Board-Folk/TRS80IUS/v1.1/Kicad/TR80IUS_VRAM.kicad_sch

## KiCad design v1.1/Kicad/TR80IUS_VRAM.kicad_sch (2023-12-29)

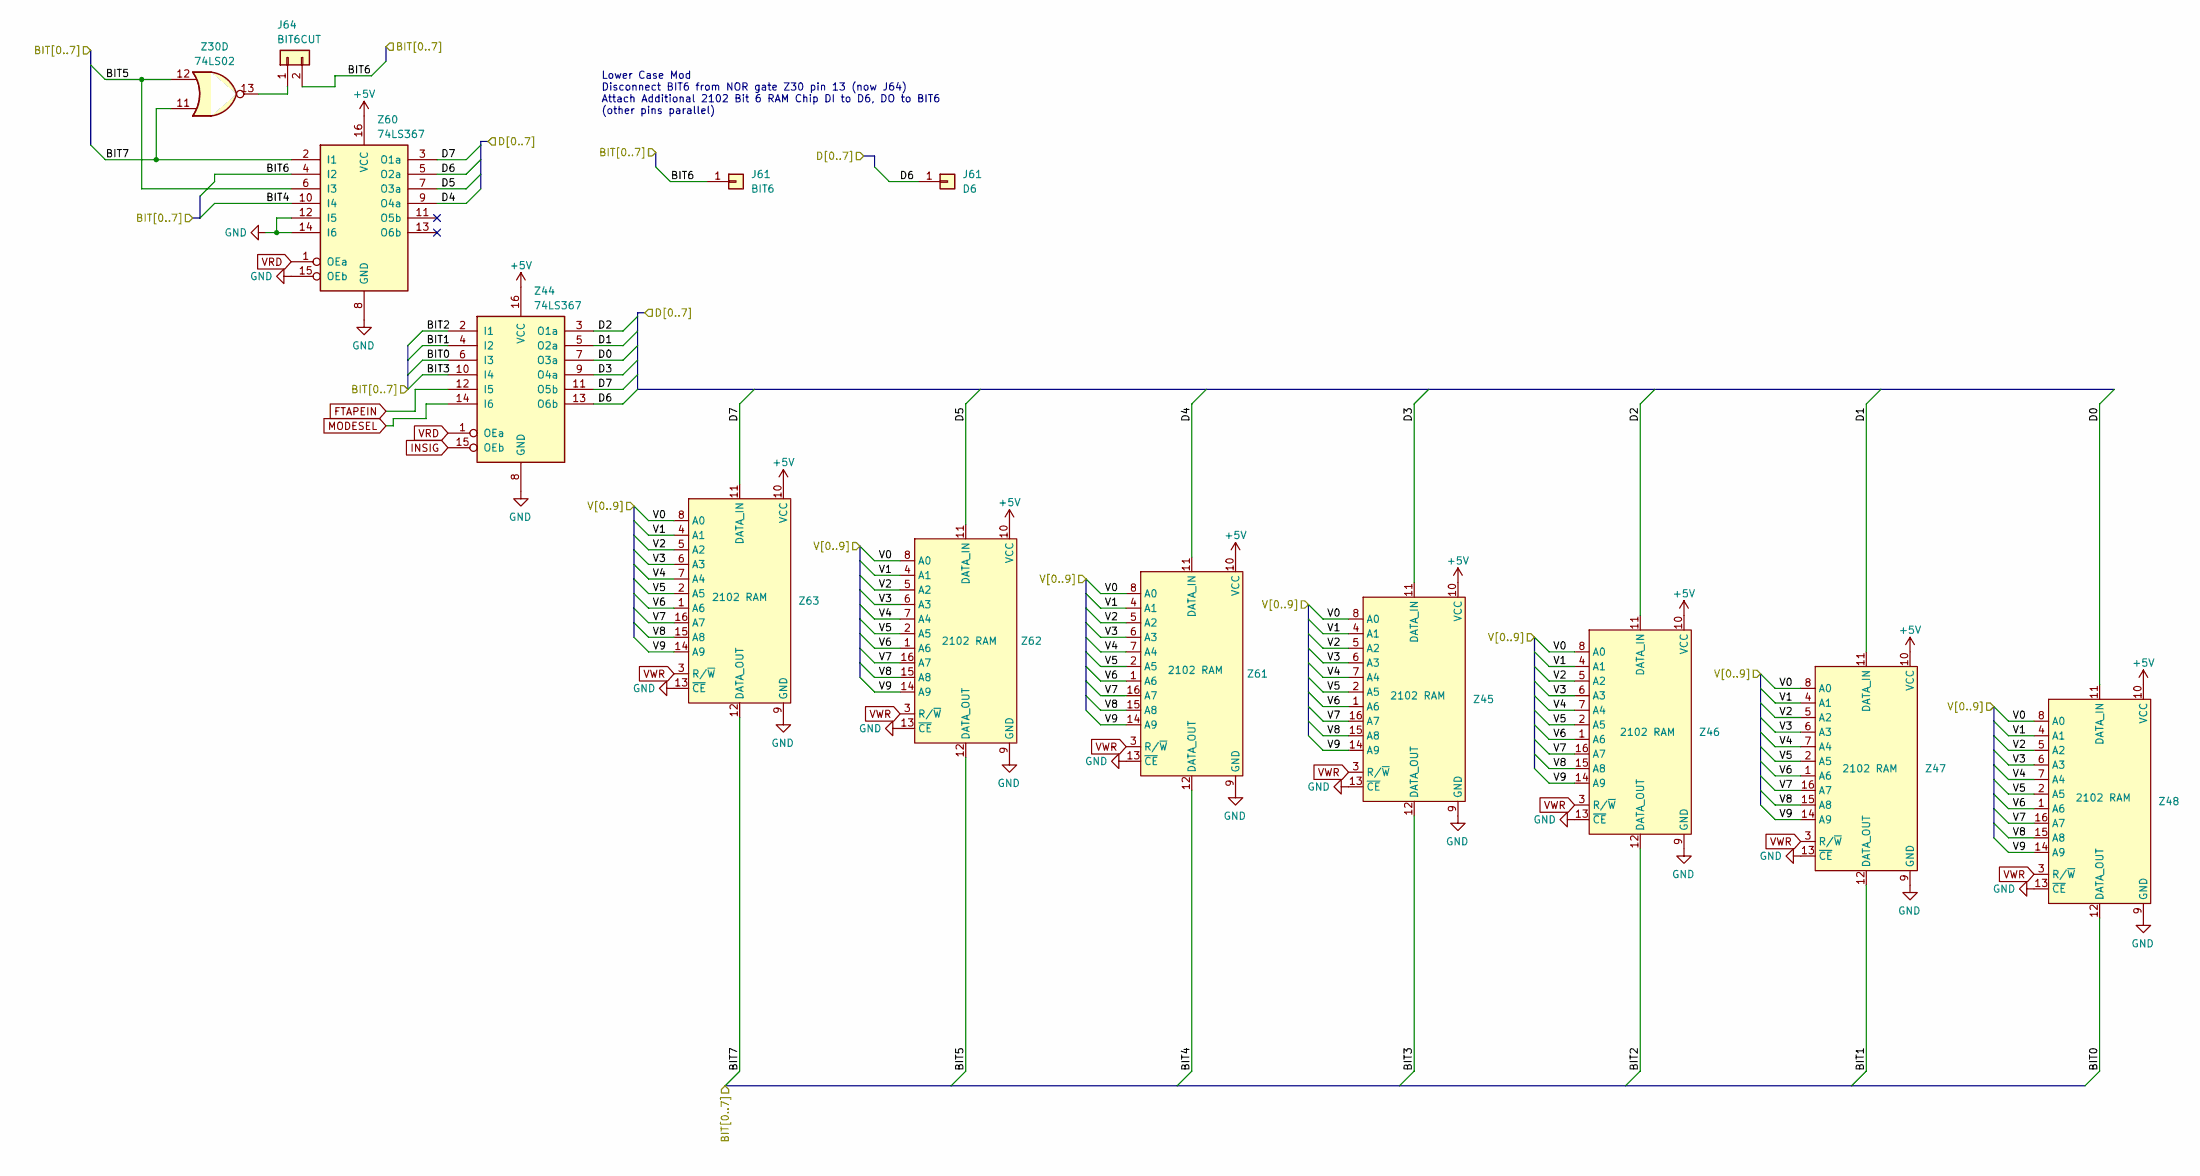
[picture p6: schematic TR80IUS_VRAM.kicad_sch]

Parts:
J61: BIT6; MODHEADER
J64: BIT6CUT; Jumper
Z30: 74LS02; DIP-14_W7.62mm
Z44, Z60: 74LS367; DIP-16_W7.62mm
Z45, Z46, Z47, Z48, Z61, Z62, Z63: 2102 RAM; DIP-16_W7.62mm

Connections:
+5V: Z44.16 (VCC), Z45.10 (VCC), Z46.10 (VCC), Z47.10 (VCC), Z48.10 (VCC), Z60.16 (VCC), Z61.10 (VCC), Z62.10 (VCC), Z63.10 (VCC)
BIT0: Z44.6 (I3), Z48.12 (DATA_OUT)
BIT1: Z44.4 (I2), Z47.12 (DATA_OUT)
BIT2: Z44.2 (I1), Z46.12 (DATA_OUT)
BIT3: Z44.10 (I4), Z45.12 (DATA_OUT)
BIT4: Z60.10 (I4), Z61.12 (DATA_OUT)
BIT5: Z30.12, Z60.6 (I3), Z62.12 (DATA_OUT)
BIT6: J61.1, J64.2, Z60.4 (I2)
BIT7: Z30.11, Z60.2 (I1), Z63.12 (DATA_OUT)
D0: Z44.7 (O3a), Z48.11 (DATA_IN)
D1: Z44.5 (O2a), Z47.11 (DATA_IN)
D2: Z44.3 (O1a), Z46.11 (DATA_IN)
D3: Z44.9 (O4a), Z45.11 (DATA_IN)
D4: Z60.9 (O4a), Z61.11 (DATA_IN)
D5: Z60.7 (O3a), Z62.11 (DATA_IN)
D6: J61.1, Z44.13 (O6b), Z60.5 (O2a)
D7: Z44.11 (O5b), Z60.3 (O1a), Z63.11 (DATA_IN)
FTAPEIN: Z44.12 (I5)
GND: Z44.8 (GND), Z45.9 (GND), Z45.13 (~CE), Z46.9 (GND), Z46.13 (~CE), Z47.9 (GND), Z47.13 (~CE), Z48.9 (GND), Z48.13 (~CE), Z60.8 (GND), Z60.12 (I5), Z60.14 (I6), Z60.15 (OEb), Z61.9 (GND), Z61.13 (~CE), Z62.9 (GND), Z62.13 (~CE), Z63.9 (GND), Z63.13 (~CE)
INSIG: Z44.15 (OEb)
MODESEL: Z44.14 (I6)
unnamed: J64.1, Z30.13
V0: Z45.8 (A0), Z46.8 (A0), Z47.8 (A0), Z48.8 (A0), Z61.8 (A0), Z62.8 (A0), Z63.8 (A0)
V1: Z45.4 (A1), Z46.4 (A1), Z47.4 (A1), Z48.4 (A1), Z61.4 (A1), Z62.4 (A1), Z63.4 (A1)
V2: Z45.5 (A2), Z46.5 (A2), Z47.5 (A2), Z48.5 (A2), Z61.5 (A2), Z62.5 (A2), Z63.5 (A2)
V3: Z45.6 (A3), Z46.6 (A3), Z47.6 (A3), Z48.6 (A3), Z61.6 (A3), Z62.6 (A3), Z63.6 (A3)
V4: Z45.7 (A4), Z46.7 (A4), Z47.7 (A4), Z48.7 (A4), Z61.7 (A4), Z62.7 (A4), Z63.7 (A4)
V5: Z45.2 (A5), Z46.2 (A5), Z47.2 (A5), Z48.2 (A5), Z61.2 (A5), Z62.2 (A5), Z63.2 (A5)
V6: Z45.1 (A6), Z46.1 (A6), Z47.1 (A6), Z48.1 (A6), Z61.1 (A6), Z62.1 (A6), Z63.1 (A6)
V7: Z45.16 (A7), Z46.16 (A7), Z47.16 (A7), Z48.16 (A7), Z61.16 (A7), Z62.16 (A7), Z63.16 (A7)
V8: Z45.15 (A8), Z46.15 (A8), Z47.15 (A8), Z48.15 (A8), Z61.15 (A8), Z62.15 (A8), Z63.15 (A8)
V9: Z45.14 (A9), Z46.14 (A9), Z47.14 (A9), Z48.14 (A9), Z61.14 (A9), Z62.14 (A9), Z63.14 (A9)
VRD: Z44.1 (OEa), Z60.1 (OEa)
VWR: Z45.3 (R/~W), Z46.3 (R/~W), Z47.3 (R/~W), Z48.3 (R/~W), Z61.3 (R/~W), Z62.3 (R/~W), Z63.3 (R/~W)

Notes on the sheet:
Lower Case Mod Disconnect BIT6 from NOR gate Z30 pin 13 (now J64) Attach Additional 2102 Bit 6 RAM Chip DI to D6, DO to BIT6 (other pins parallel)
