Board-Folk/TRS80IUS/v1.1/Kicad/TRS80IUS.kicad_sch

## KiCad design v1.1/Kicad/TRS80IUS.kicad_sch (2023-12-29)

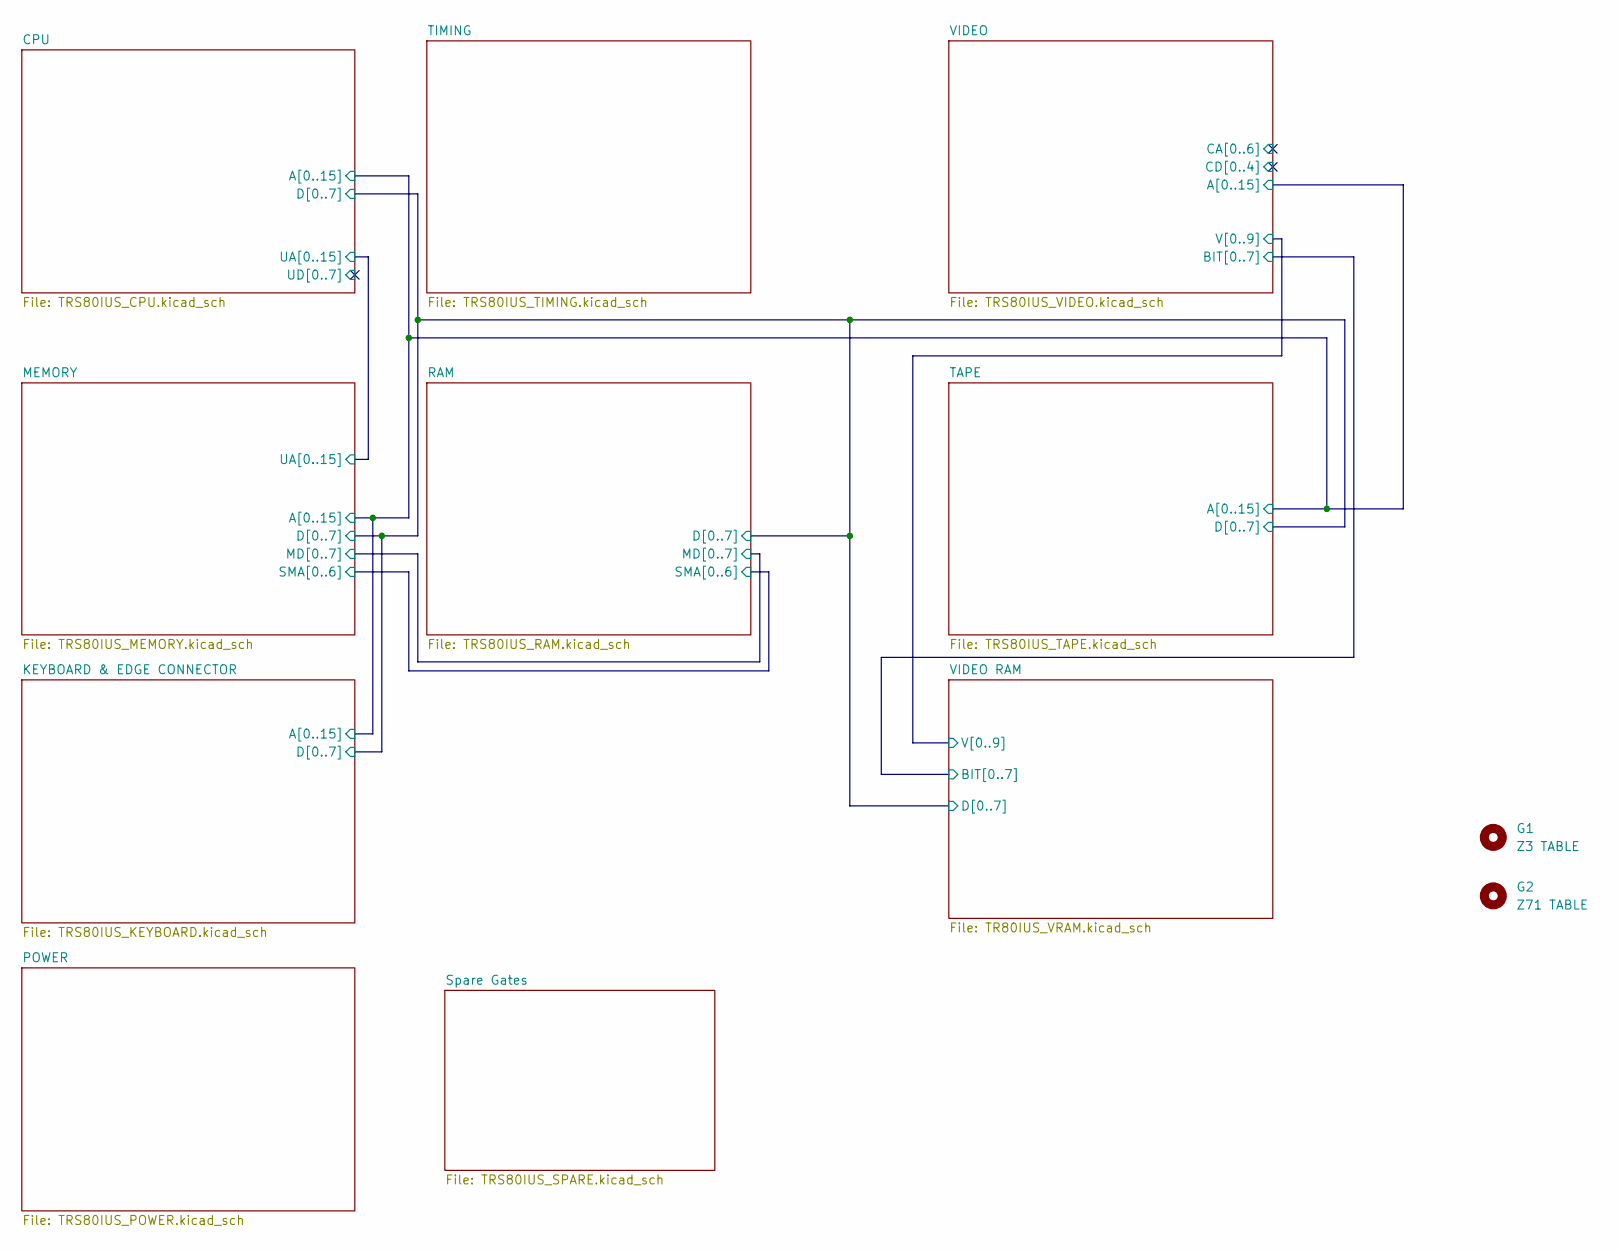
[picture p7: schematic TRS80IUS.kicad_sch]

Parts:
G1: Z3 TABLE; Z3TABLE
G2: Z71 TABLE; Z71TABLE
