Board-Folk/TRS80IUS/v1.1/Kicad/TRS80IUS_CPU.kicad_sch

## KiCad design v1.1/Kicad/TRS80IUS_CPU.kicad_sch (2023-12-29)

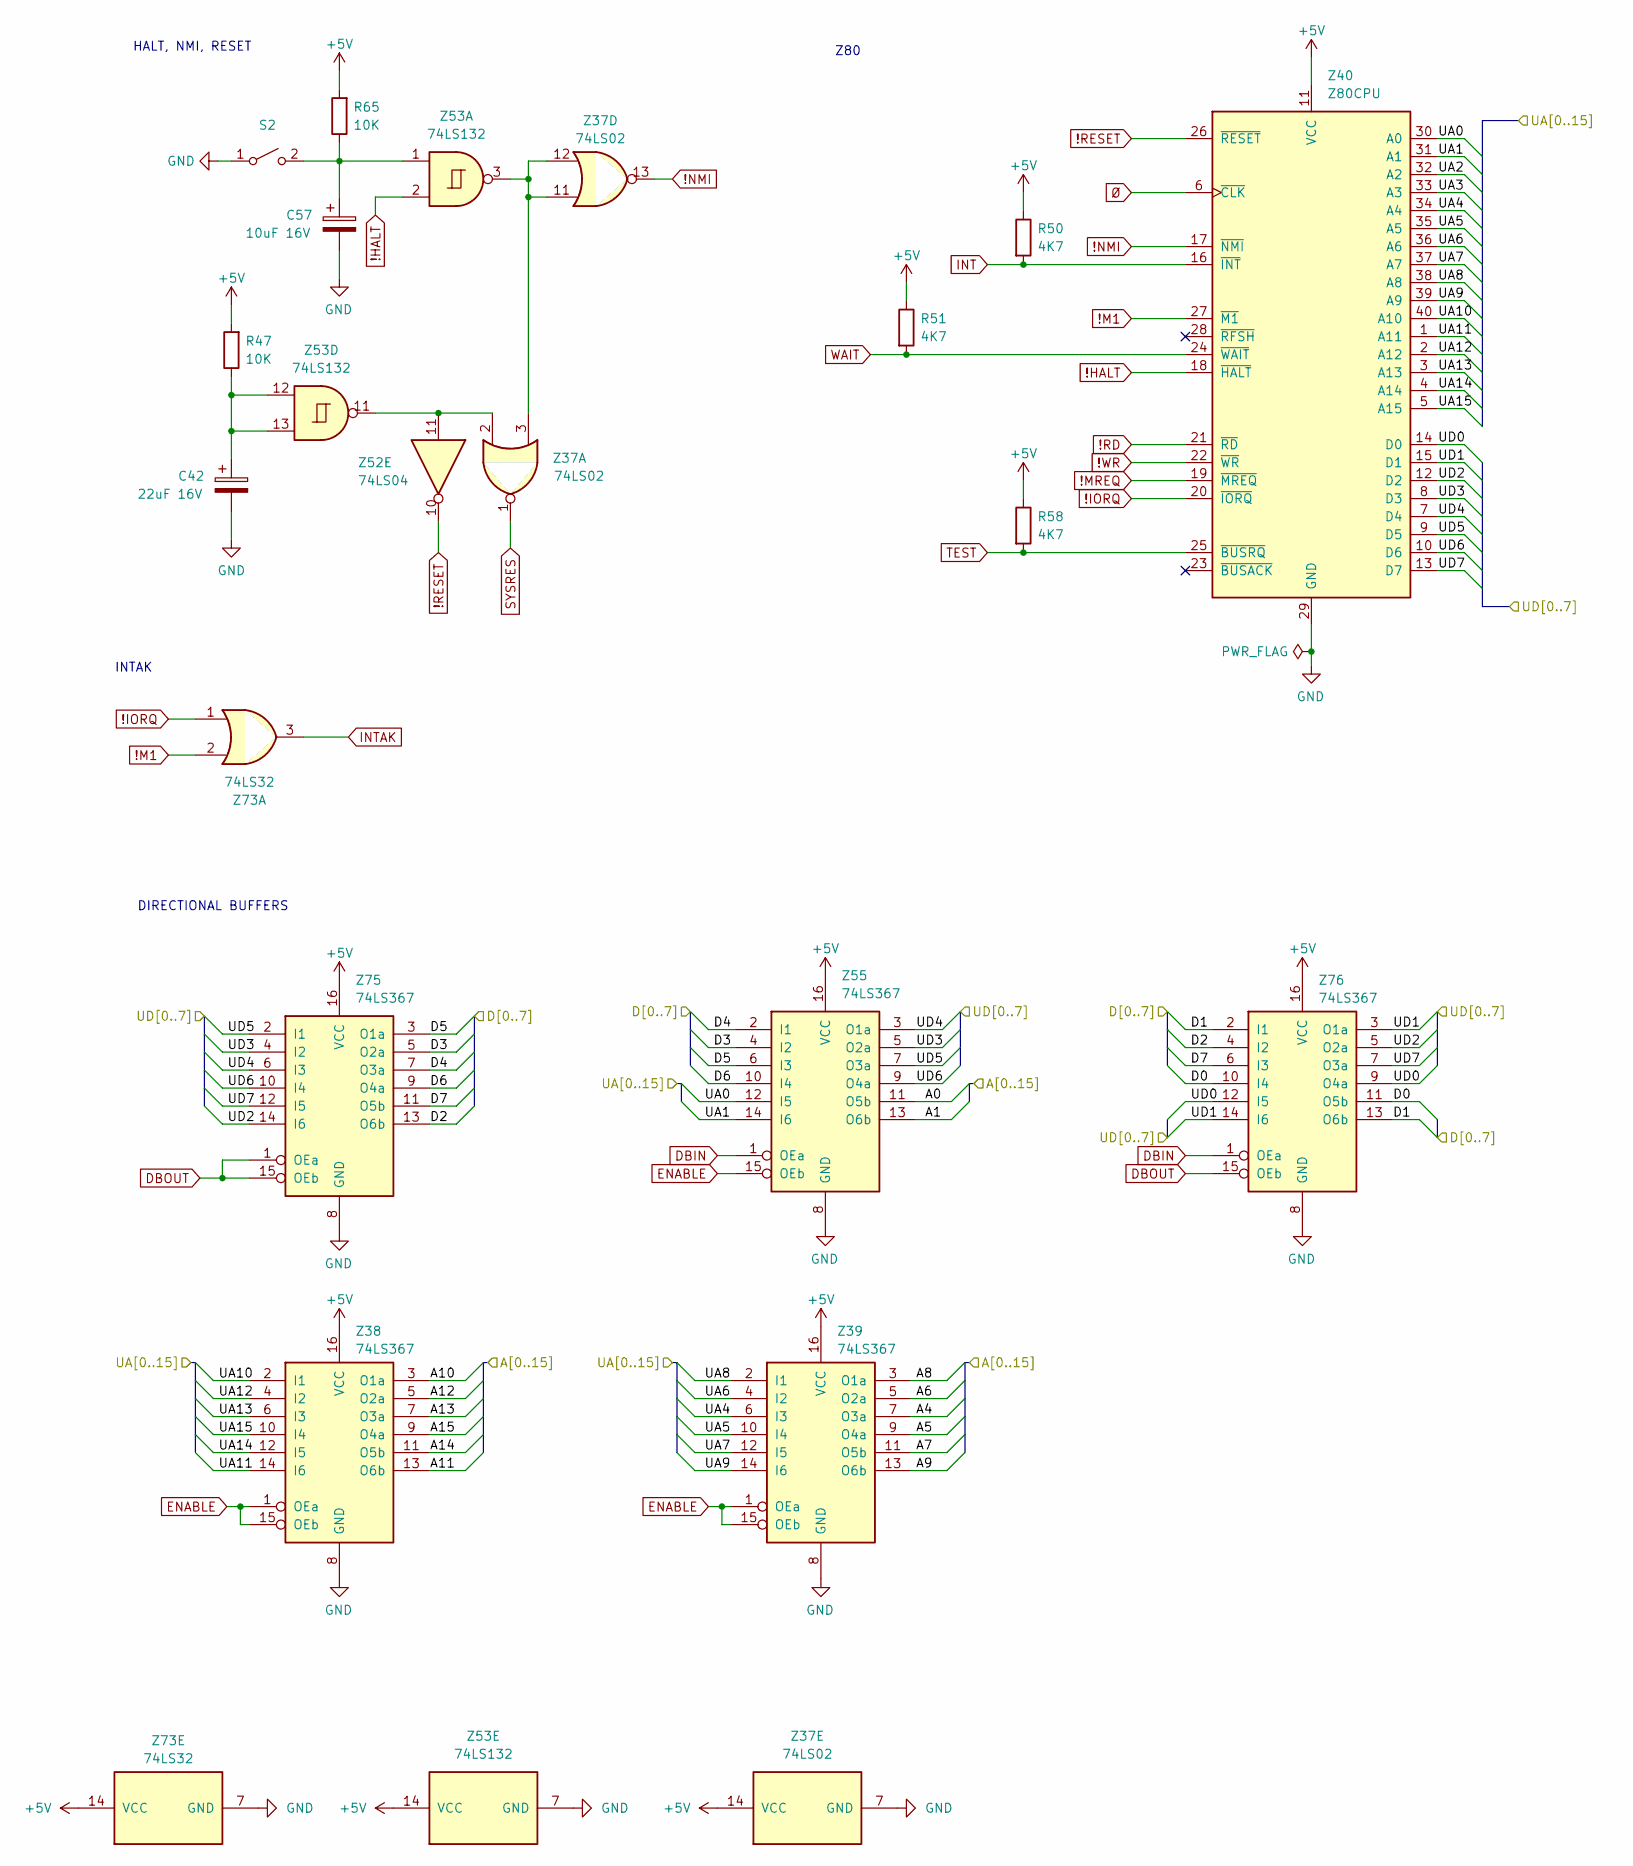
[picture p8: schematic TRS80IUS_CPU.kicad_sch]

Parts:
C42: 22uF 16V; Electrolytic Cap 2.5mm
C57: 10uF 16V; Electrolytic Cap 2.5mm
R47, R65: 10K; Resistor 12.7mm
R50, R51, R58: 4K7; Resistor 12.7mm
S2: RESET; S2 - 4mm
Z37: 74LS02; DIP-14_W7.62mm
Z38, Z39, Z55, Z75, Z76: 74LS367; DIP-16_W7.62mm
Z40: Z80CPU; DIP-40_W15.24mm
Z52: 74LS04; DIP-14_W7.62mm
Z53: 74LS132; DIP-14_W7.62mm
Z73: 74LS32; DIP-14_W7.62mm

Connections:
!HALT: Z40.18 (~HALT), Z53.2
!IORQ: Z40.20 (~IORQ), Z73.1
!M1: Z40.27 (~M1), Z73.2
!MREQ: Z40.19 (~MREQ)
!NMI: Z37.13, Z40.17 (~NMI)
!RD: Z40.21 (~RD)
!RESET: Z40.26 (~RESET), Z52.10
!WR: Z40.22 (~WR)
+5V: R47.2, R50.1, R51.1, R58.1, R65.2, Z37.14 (VCC), Z38.16 (VCC), Z39.16 (VCC), Z40.11 (VCC), Z53.14 (VCC), Z55.16 (VCC), Z73.14 (VCC), Z75.16 (VCC), Z76.16 (VCC)
A0: Z55.11 (O5b)
A1: Z55.13 (O6b)
A4: Z39.7 (O3a)
A5: Z39.9 (O4a)
A6: Z39.5 (O2a)
A7: Z39.11 (O5b)
A8: Z39.3 (O1a)
A9: Z39.13 (O6b)
A10: Z38.3 (O1a)
A11: Z38.13 (O6b)
A12: Z38.5 (O2a)
A13: Z38.7 (O3a)
A14: Z38.11 (O5b)
A15: Z38.9 (O4a)
D0: Z76.10 (I4), Z76.11 (O5b)
D1: Z76.2 (I1), Z76.13 (O6b)
D2: Z75.13 (O6b), Z76.4 (I2)
D3: Z55.4 (I2), Z75.5 (O2a)
D4: Z55.2 (I1), Z75.7 (O3a)
D5: Z55.6 (I3), Z75.3 (O1a)
D6: Z55.10 (I4), Z75.9 (O4a)
D7: Z75.11 (O5b), Z76.6 (I3)
DBIN: Z55.1 (OEa), Z76.1 (OEa)
DBOUT: Z75.1 (OEa), Z75.15 (OEb), Z76.15 (OEb)
ENABLE: Z38.1 (OEa), Z38.15 (OEb), Z39.1 (OEa), Z39.15 (OEb), Z55.15 (OEb)
GND: C42.2, C57.2, S2.1 (A), Z37.7 (GND), Z38.8 (GND), Z39.8 (GND), Z40.29 (GND), Z53.7 (GND), Z55.8 (GND), Z73.7 (GND), Z75.8 (GND), Z76.8 (GND)
INT: R50.2, Z40.16 (~INT)
INTAK: Z73.3
unnamed: C42.1, R47.1, Z53.12, Z53.13
unnamed: C57.1, R65.1, S2.2 (B), Z53.1
unnamed: Z37.2, Z52.11, Z53.11
unnamed: Z37.3, Z37.11, Z37.12, Z53.3
SYSRES: Z37.1
TEST: R58.2, Z40.25 (~BUSRQ)
UA0: Z40.30 (A0), Z55.12 (I5)
UA1: Z40.31 (A1), Z55.14 (I6)
UA2: Z40.32 (A2)
UA3: Z40.33 (A3)
UA4: Z39.6 (I3), Z40.34 (A4)
UA5: Z39.10 (I4), Z40.35 (A5)
UA6: Z39.4 (I2), Z40.36 (A6)
UA7: Z39.12 (I5), Z40.37 (A7)
UA8: Z39.2 (I1), Z40.38 (A8)
UA9: Z39.14 (I6), Z40.39 (A9)
UA10: Z38.2 (I1), Z40.40 (A10)
UA11: Z38.14 (I6), Z40.1 (A11)
UA12: Z38.4 (I2), Z40.2 (A12)
UA13: Z38.6 (I3), Z40.3 (A13)
UA14: Z38.12 (I5), Z40.4 (A14)
UA15: Z38.10 (I4), Z40.5 (A15)
UD0: Z40.14 (D0), Z76.9 (O4a), Z76.12 (I5)
UD1: Z40.15 (D1), Z76.3 (O1a), Z76.14 (I6)
UD2: Z40.12 (D2), Z75.14 (I6), Z76.5 (O2a)
UD3: Z40.8 (D3), Z55.5 (O2a), Z75.4 (I2)
UD4: Z40.7 (D4), Z55.3 (O1a), Z75.6 (I3)
UD5: Z40.9 (D5), Z55.7 (O3a), Z75.2 (I1)
UD6: Z40.10 (D6), Z55.9 (O4a), Z75.10 (I4)
UD7: Z40.13 (D7), Z75.12 (I5), Z76.7 (O3a)
WAIT: R51.2, Z40.24 (~WAIT)
Ø: Z40.6 (~CLK)

Notes on the sheet:
HALT, NMI, RESET
INTAK
DIRECTIONAL BUFFERS
Z80
