Board-Folk/TRS80IUS/v1.1/Kicad/TRS80IUS_KEYBOARD.kicad_sch

## KiCad design v1.1/Kicad/TRS80IUS_KEYBOARD.kicad_sch (2023-12-29)

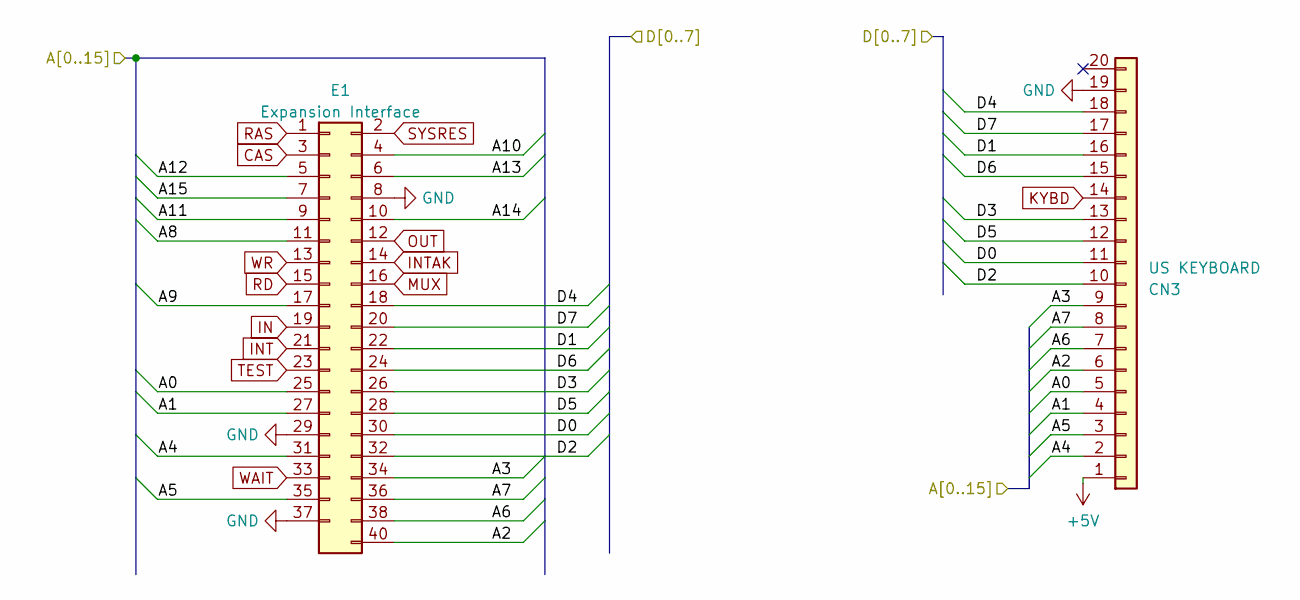
[picture p9: schematic TRS80IUS_KEYBOARD.kicad_sch]

Parts:
CN3: US KEYBOARD; Keyboard 2.54mm
E1: Expansion Interface; TRS80IEdgeConnector

Connections:
+5V: CN3.1
A0: CN3.5, E1.25
A1: CN3.4, E1.27
A2: CN3.6, E1.40
A3: CN3.9, E1.34
A4: CN3.2, E1.31
A5: CN3.3, E1.35
A6: CN3.7, E1.38
A7: CN3.8, E1.36
A8: E1.11
A9: E1.17
A10: E1.4
A11: E1.9
A12: E1.5
A13: E1.6
A14: E1.10
A15: E1.7
CAS: E1.3
D0: CN3.11, E1.30
D1: CN3.16, E1.22
D2: CN3.10, E1.32
D3: CN3.13, E1.26
D4: CN3.18, E1.18
D5: CN3.12, E1.28
D6: CN3.15, E1.24
D7: CN3.17, E1.20
GND: CN3.19, E1.8, E1.29, E1.37
IN: E1.19
INT: E1.21
INTAK: E1.14
KYBD: CN3.14
MUX: E1.16
OUT: E1.12
RAS: E1.1
RD: E1.15
SYSRES: E1.2
TEST: E1.23
WAIT: E1.33
WR: E1.13
