Board-Folk/TRS80IUS/v1.1/Kicad/TRS80IUS_MEMORY.kicad_sch

## KiCad design v1.1/Kicad/TRS80IUS_MEMORY.kicad_sch (2023-12-29)

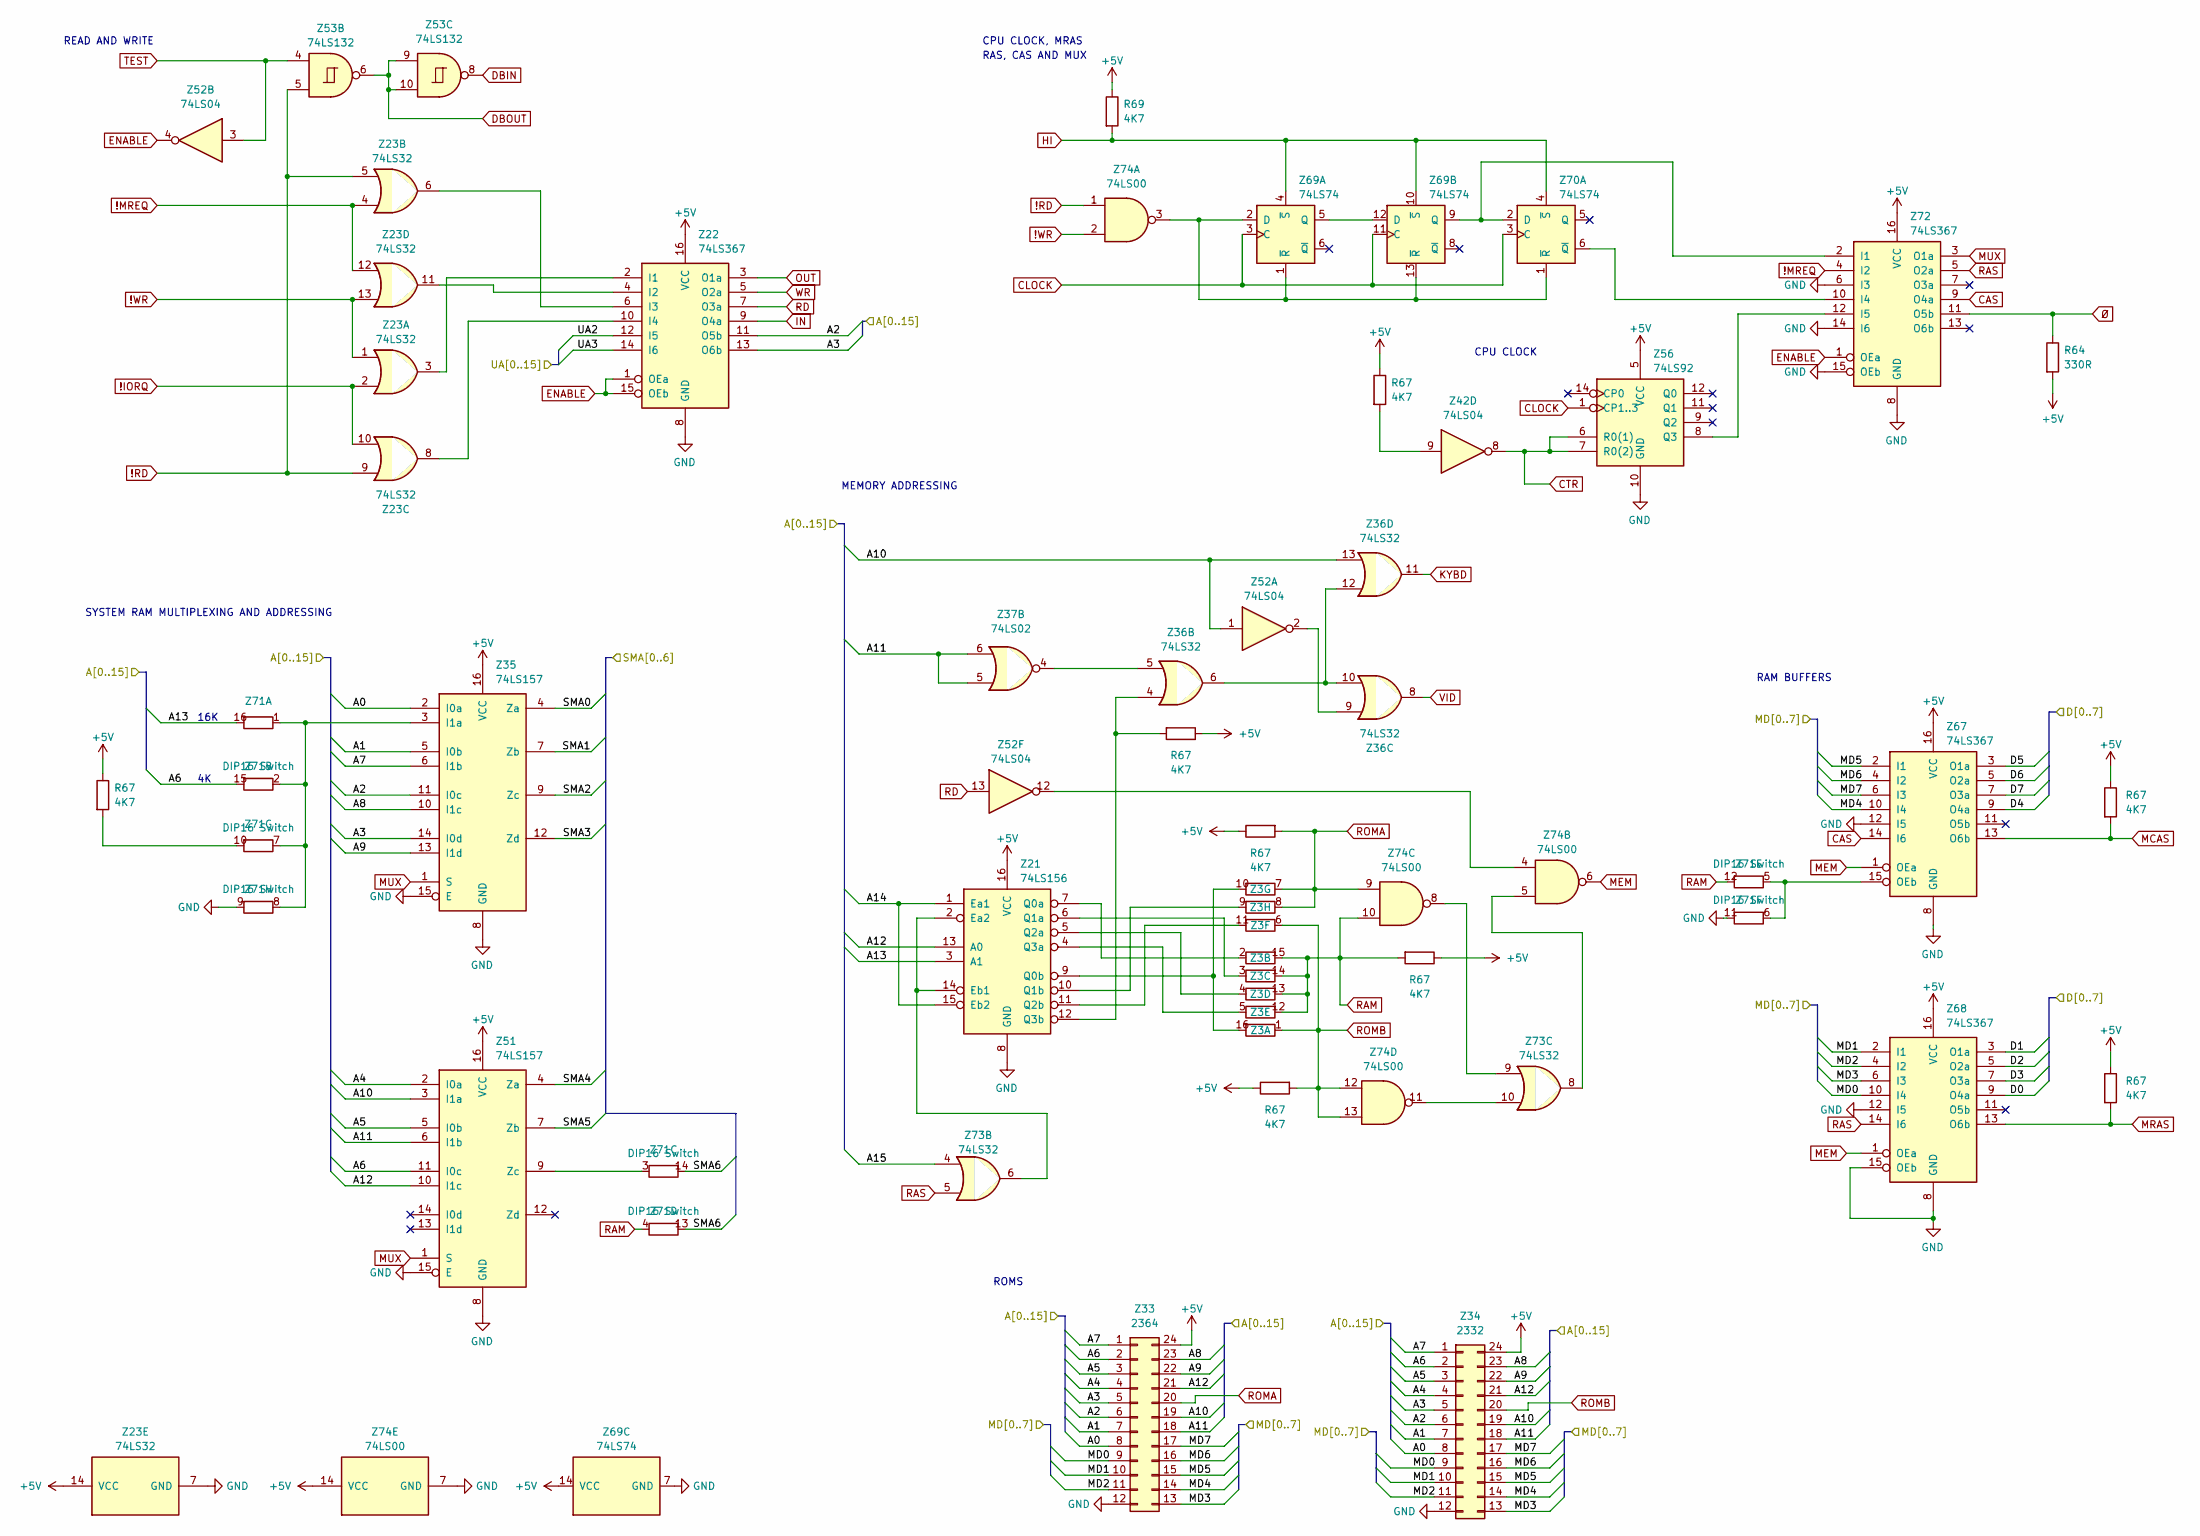
[picture p10: schematic TRS80IUS_MEMORY.kicad_sch]

Parts:
R64: 330R; Resistor 12.7mm
R67, R69: 4K7; Resistor 12.7mm
Z3, Z71: DIP16 Switch; DIP-16_W7.62mm
Z21: 74LS156; DIP-16_W7.62mm
Z22, Z67, Z68, Z72: 74LS367; DIP-16_W7.62mm
Z23, Z36, Z73: 74LS32; DIP-14_W7.62mm
Z33: 2364; DIP-24_W15.24mm
Z34: 2332; DIP-24_W15.24mm
Z35, Z51: 74LS157; DIP-16_W7.62mm
Z37: 74LS02; DIP-14_W7.62mm
Z42, Z52: 74LS04; DIP-14_W7.62mm
Z53: 74LS132; DIP-14_W7.62mm
Z56: 74LS92; DIP-14_W7.62mm
Z69, Z70: 74LS74; DIP-14_W7.62mm
Z74: 74LS00; DIP-14_W7.62mm

Connections:
!IORQ: Z23.2, Z23.10
!MREQ: Z23.4, Z23.12, Z72.4 (I2)
!RD: Z23.5, Z23.9, Z53.5, Z74.1
!WR: Z23.1, Z23.13, Z74.2
+5V: R64.2, R67.1, R69.1, Z21.16 (VCC), Z22.16 (VCC), Z23.14 (VCC), Z33.24, Z34.24, Z35.16 (VCC), Z51.16 (VCC), Z56.5 (VCC), Z67.16 (VCC), Z68.16 (VCC), Z69.14 (VCC), Z72.16 (VCC), Z74.14 (VCC)
A0: Z33.8, Z34.8, Z35.2 (I0a)
A1: Z33.7, Z34.7, Z35.5 (I0b)
A2: Z22.11 (O5b), Z33.6, Z34.6, Z35.11 (I0c)
A3: Z22.13 (O6b), Z33.5, Z34.5, Z35.14 (I0d)
A4: Z33.4, Z34.4, Z51.2 (I0a)
A5: Z33.3, Z34.3, Z51.5 (I0b)
A6: Z33.2, Z34.2, Z51.11 (I0c), Z71.15 (R2.2)
A7: Z33.1, Z34.1, Z35.6 (I1b)
A8: Z33.23, Z34.23, Z35.10 (I1c)
A9: Z33.22, Z34.22, Z35.13 (I1d)
A10: Z33.19, Z34.19, Z36.13, Z51.3 (I1a), Z52.1
A11: Z33.18, Z34.18, Z37.5, Z37.6, Z51.6 (I1b)
A12: Z21.13 (A0), Z33.21, Z34.21, Z51.10 (I1c)
A13: Z21.3 (A1), Z71.16 (R1.2)
A14: Z21.1 (Ea1), Z21.15 (Eb2)
A15: Z73.4
CAS: Z67.14 (I6), Z72.9 (O4a)
CLOCK: Z56.1 (CP1..3), Z69.3 (C), Z69.11 (C), Z70.3 (C)
CTR: Z42.8, Z56.6 (R0(1)), Z56.7 (R0(2))
D0: Z68.9 (O4a)
D1: Z68.3 (O1a)
D2: Z68.5 (O2a)
D3: Z68.7 (O3a)
D4: Z67.9 (O4a)
D5: Z67.3 (O1a)
D6: Z67.5 (O2a)
D7: Z67.7 (O3a)
DBIN: Z53.8
DBOUT: Z53.6, Z53.9, Z53.10
ENABLE: Z22.1 (OEa), Z22.15 (OEb), Z52.4, Z72.1 (OEa)
GND: Z21.8 (GND), Z22.8 (GND), Z23.7 (GND), Z33.12, Z34.12, Z35.8 (GND), Z35.15 (E), Z51.8 (GND), Z51.15 (E), Z56.10 (GND), Z67.8 (GND), Z67.12 (I5), Z68.8 (GND), Z68.12 (I5), Z68.15 (OEb), Z69.7 (GND), Z71.9 (R8.2), Z71.11 (R6.2), Z72.6 (I3), Z72.8 (GND), Z72.14 (I6), Z72.15 (OEb), Z74.7 (GND)
HI: R69.2, Z69.4 (~S), Z69.10 (~S), Z70.4 (~S)
IN: Z22.9 (O4a)
KYBD: Z36.11
MCAS: R67.2, Z67.13 (O6b)
MD0: Z33.9, Z34.9, Z68.10 (I4)
MD1: Z33.10, Z34.10, Z68.2 (I1)
MD2: Z33.11, Z34.11, Z68.4 (I2)
MD3: Z33.13, Z34.13, Z68.6 (I3)
MD4: Z33.14, Z34.14, Z67.10 (I4)
MD5: Z33.15, Z34.15, Z67.2 (I1)
MD6: Z33.16, Z34.16, Z67.4 (I2)
MD7: Z33.17, Z34.17, Z67.6 (I3)
MEM: Z67.1 (OEa), Z68.1 (OEa), Z74.6
MRAS: R67.2, Z68.13 (O6b)
MUX: Z35.1 (S), Z51.1 (S), Z72.3 (O1a)
unnamed: R67.2, Z21.12 (Q3b), Z36.4, Z42.9, Z71.10 (R7.2)
unnamed: Z3.5 (R5.1), Z21.4 (Q3a)
unnamed: Z3.4 (R4.1), Z21.5 (Q2a)
unnamed: Z3.3 (R3.1), Z21.6 (Q1a)
unnamed: Z3.2 (R2.1), Z21.7 (Q0a)
unnamed: Z3.10 (R7.2), Z3.16 (R1.2), Z21.9 (Q0b)
unnamed: Z3.9 (R8.2), Z21.10 (Q1b)
unnamed: Z3.11 (R6.2), Z21.11 (Q2b)
unnamed: Z21.2 (Ea2), Z21.14 (Eb1), Z73.6
unnamed: Z22.2 (I1), Z23.3
unnamed: Z22.4 (I2), Z23.11
unnamed: Z22.6 (I3), Z23.6
unnamed: Z22.10 (I4), Z23.8
unnamed: Z35.3 (I1a), Z71.1 (R1.1), Z71.2 (R2.1), Z71.7 (R7.1), Z71.8 (R8.1)
unnamed: Z36.5, Z37.4
unnamed: Z36.9, Z52.2
unnamed: Z36.6, Z36.10, Z36.12
unnamed: Z51.9 (Zc), Z71.3 (R3.1)
unnamed: Z52.12, Z74.4
unnamed: Z56.8 (Q3), Z72.12 (I5)
unnamed: Z67.15 (OEb), Z71.5 (R5.1), Z71.6 (R6.1)
unnamed: Z69.1 (~R), Z69.2 (D), Z69.13 (~R), Z70.1 (~R), Z74.3
unnamed: Z69.9 (Q), Z70.2 (D), Z72.2 (I1)
unnamed: Z69.5 (Q), Z69.12 (D)
unnamed: Z70.6 (~Q), Z72.10 (I4)
unnamed: Z73.8, Z74.5
unnamed: Z73.9, Z74.8
unnamed: Z73.10, Z74.11
OUT: Z22.3 (O1a)
RAM: R67.2, Z3.12 (R5.2), Z3.13 (R4.2), Z3.14 (R3.2), Z3.15 (R2.2), Z71.4 (R4.1), Z71.12 (R5.2), Z74.10
RAS: Z68.14 (I6), Z72.5 (O2a), Z73.5
RD: Z22.7 (O3a), Z52.13
ROMA: R67.2, Z3.7 (R7.1), Z3.8 (R8.1), Z33.20, Z74.9
ROMB: R67.2, Z3.1 (R1.1), Z3.6 (R6.1), Z34.20, Z74.12, Z74.13
SMA0: Z35.4 (Za)
SMA1: Z35.7 (Zb)
SMA2: Z35.9 (Zc)
SMA3: Z35.12 (Zd)
SMA4: Z51.4 (Za)
SMA5: Z51.7 (Zb)
SMA6: Z71.13 (R4.2), Z71.14 (R3.2)
TEST: Z52.3, Z53.4
UA2: Z22.12 (I5)
UA3: Z22.14 (I6)
VID: Z36.8
WR: Z22.5 (O2a)
Ø: R64.1, Z72.11 (O5b)

Notes on the sheet:
CPU CLOCK
16K
RAM BUFFERS
READ AND WRITE
MEMORY ADDRESSING
RAS, CAS AND MUX
SYSTEM RAM MULTIPLEXING AND ADDRESSING
ROMS
CPU CLOCK, MRAS
