Board-Folk/TRS80IUS/v1.1/Kicad/TRS80IUS_POWER.kicad_sch

## KiCad design v1.1/Kicad/TRS80IUS_POWER.kicad_sch (2023-12-29)

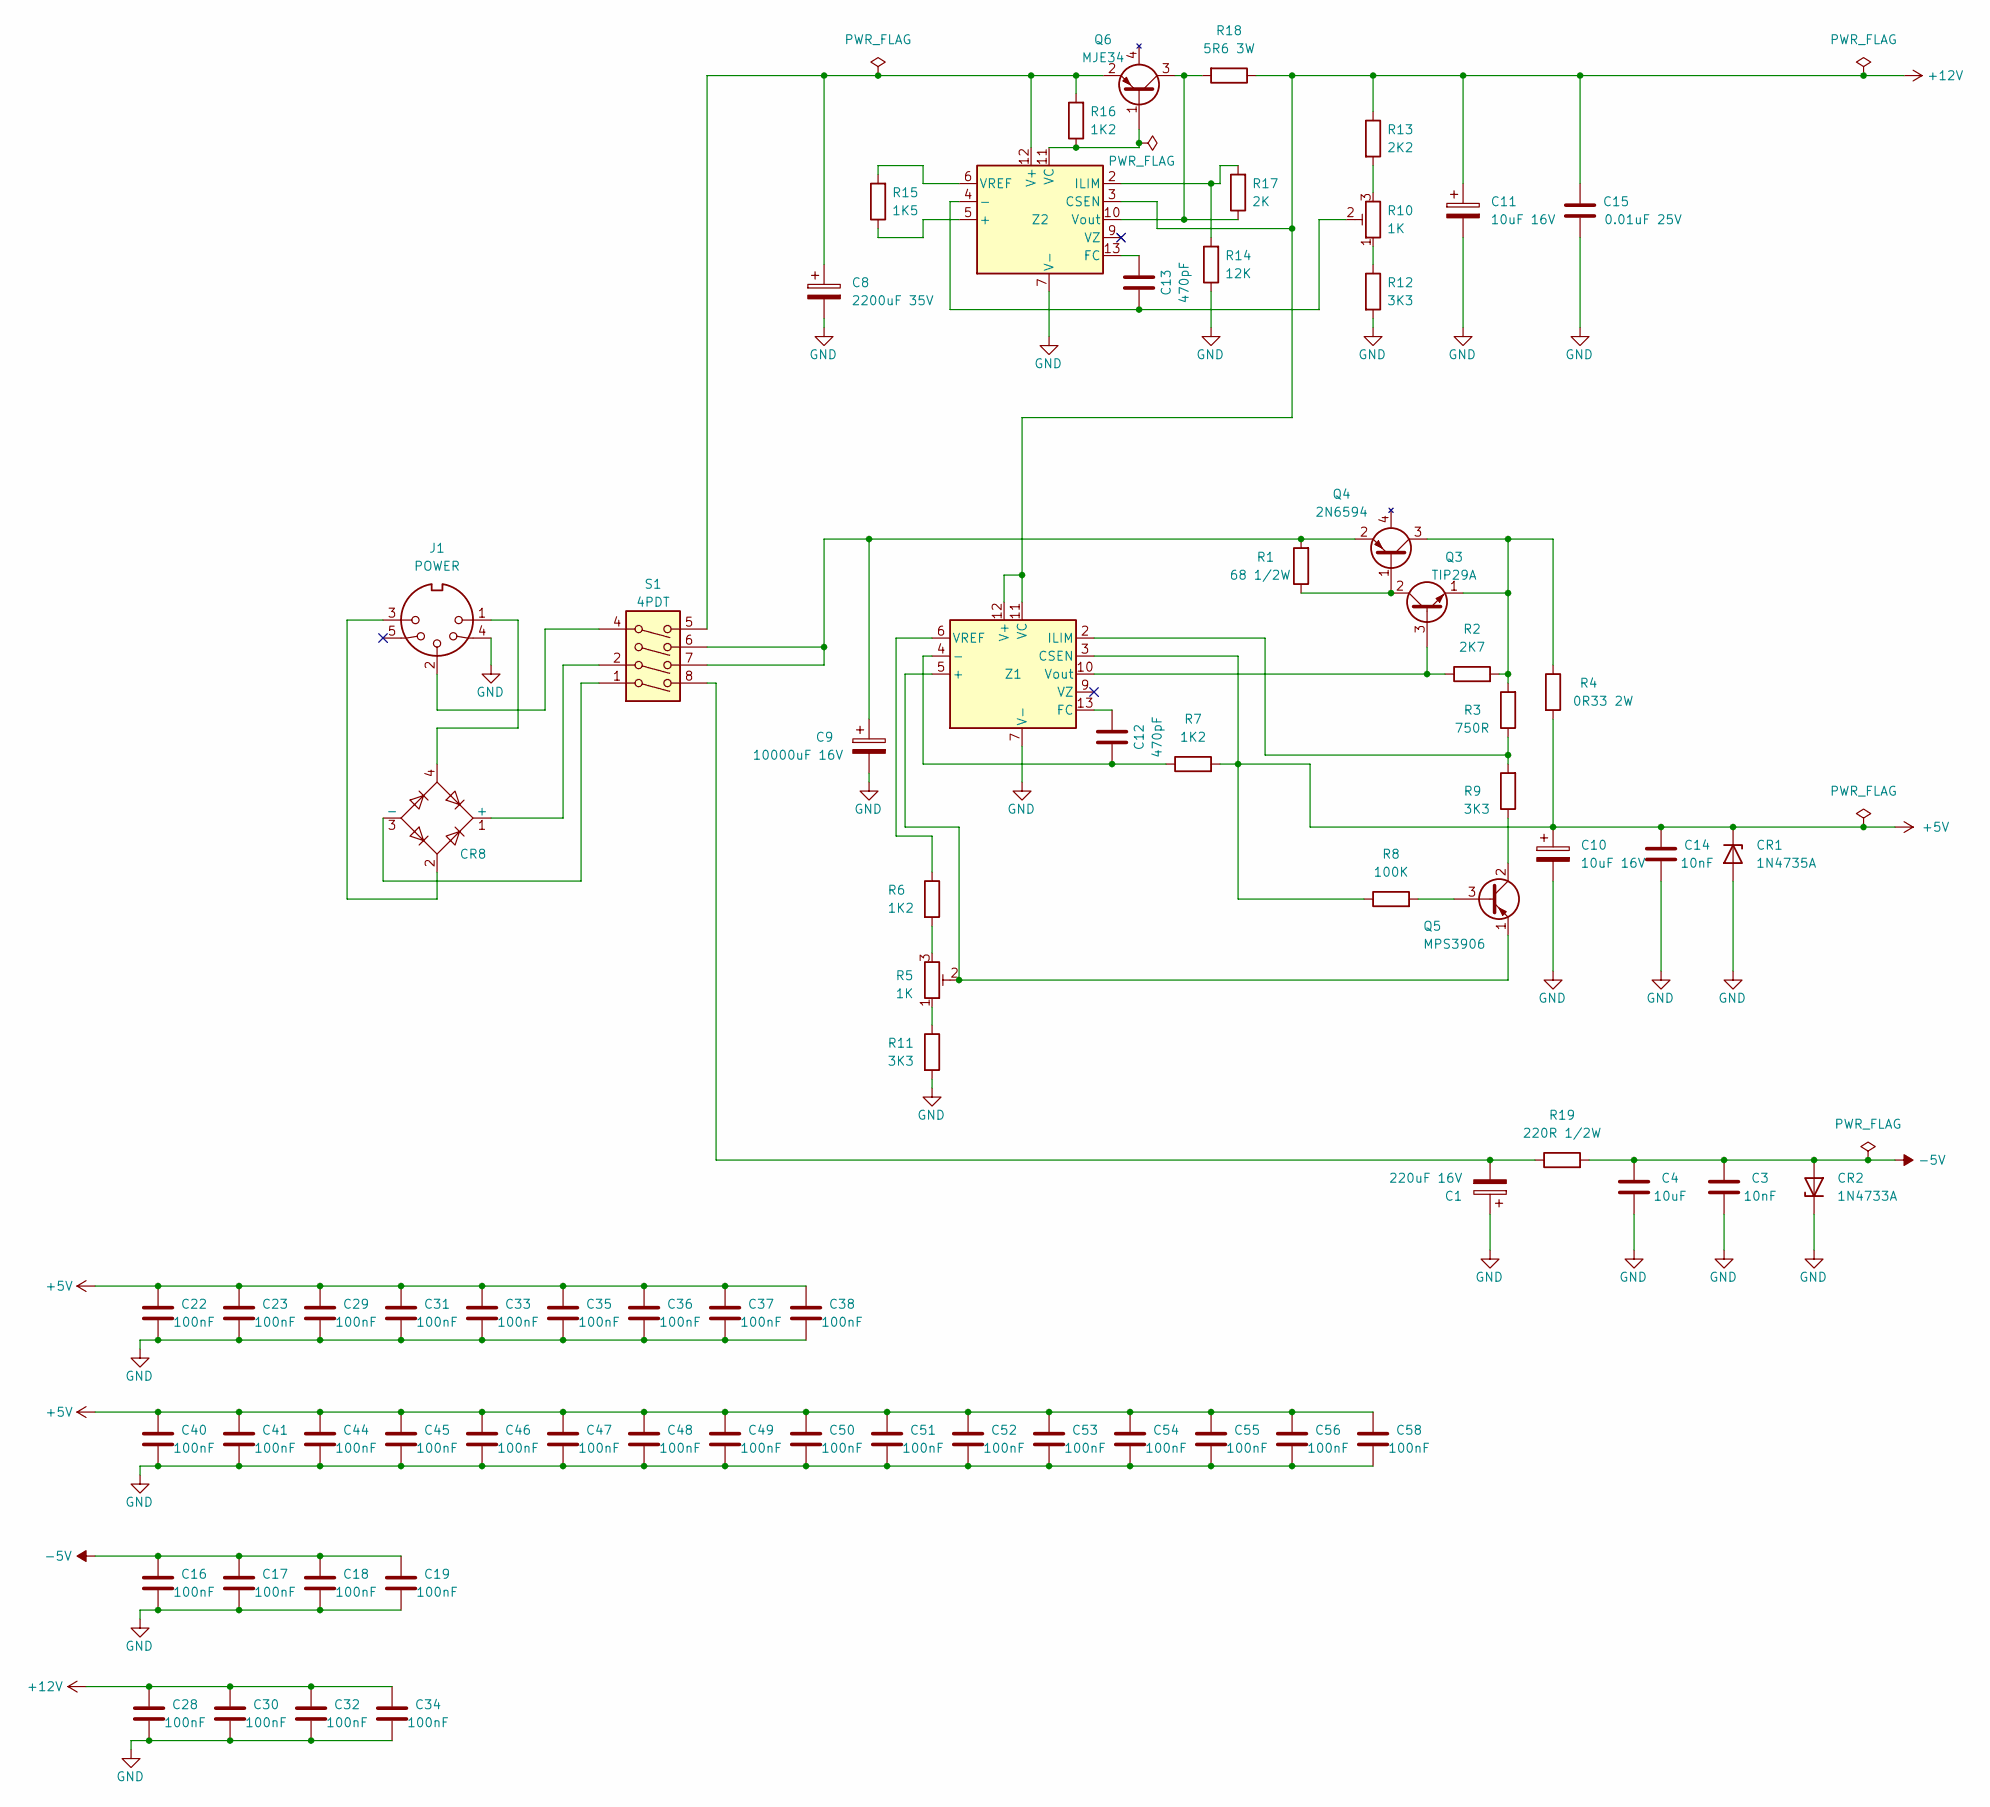
[picture p11: schematic TRS80IUS_POWER.kicad_sch]

Parts:
C1: 220uF 16V; Capacitor C1
C3, C14: 10nF; Ceramic Disc 6.35mm
C4: 10uF; Electrolytic Cap 2.5mm
C8: 2200uF 35V; Capacitor C8
C9: 10000uF 16V; Capacitor C9
C10, C11: 10uF 16V; Electrolytic Cap 2.5mm
C12, C13: 470pF; Ceramic Disc 6.35mm
C15: 0.01uF 25V; Ceramic Disc 6.35mm
C16, C17, C18, C19, C22, C23, C29, C31, C33, C35, C36, C37, C38, C40, C41, C46, C47, C48, C49, C50, C51, C52, C53, C54, C55, C56: 100nF; Ceramic Disc 6.35mm
C28, C30, C32, C34: 100nF; Ceramic Disc 9.78mm
C44, C45, C58: 100nF; Ceramic Disc 7mm
CR1: 1N4735A; Diode 12.7mm
CR2: 1N4733A; Diode 12.7mm
CR8: S2V B20; Rectifier CR8
J1: POWER; 5-Pin DIN Socket
Q3: TIP29A; Q3
Q4: 2N6594; Q4 TO-3
Q5: MPS3906; Transistor
Q6: MJE34; Transistor Q6
R1: 68 1/2W; Resistor 12.7mm
R2: 2K7; Resistor 12.7mm
R3: 750R; Resistor 12.7mm
R4: 0R33 2W; Resistor R4 23mm
R5: 1K; Pot - Alt Pins 1 and 3
R6, R7, R16: 1K2; Resistor 12.7mm
R8: 100K; Resistor 12.7mm
R9, R11, R12: 3K3; Resistor 12.7mm
R10: 1K; Pot
R13: 2K2; Resistor 12.7mm
R14: 12K; Resistor 12.7mm
R15: 1K5; Resistor 12.7mm
R17: 2K; Resistor 12.7mm
R18: 5R6 3W; Resistor R18 30.75mm
R19: 220R 1/2W; Resistor R19 15.4mm
S1: 4PDT; Switch S1 - 4mm
Z1, Z2: LM723_DIP14; DIP-14_W7.62mm

Connections:
+5V: C10.1, C14.2, C22.2, C23.2, C29.2, C31.2, C33.2, C35.2, C36.2, C37.2, C38.2, C40.2, C41.2, C44.2, C45.2, C46.2, C47.2, C48.2, C49.2, C50.2, C51.2, C52.2, C53.2, C54.2, C55.2, C56.2, C58.2, CR1.1 (K), R4.2, R7.2, R8.1, Z1.3 (CSEN)
+12V: C11.1, C15.2, C28.2, C30.2, C32.2, C34.2, R13.1, R18.1, Z1.11 (VC), Z1.12 (V+), Z2.3 (CSEN)
-5V: C3.2, C4.2, C16.2, C17.2, C18.2, C19.2, CR2.2 (A), R19.2
GND: C1.1, C3.1, C4.1, C8.2, C9.2, C10.2, C11.2, C14.1, C15.1, C16.1, C17.1, C18.1, C19.1, C22.1, C23.1, C28.1, C29.1, C30.1, C31.1, C32.1, C33.1, C34.1, C35.1, C36.1, C37.1, C38.1, C40.1, C41.1, C44.1, C45.1, C46.1, C47.1, C48.1, C49.1, C50.1, C51.1, C52.1, C53.1, C54.1, C55.1, C56.1, C58.1, CR1.2 (A), CR2.1 (K), J1.4, R11.2, R12.2, R14.1, Z1.7 (V-), Z2.7 (V-)
unnamed: C1.2, R19.1, S1.8
unnamed: C8.1, Q6.2 (E), R16.2, S1.5, Z2.12 (V+)
unnamed: C9.1, Q4.2 (E), R1.2, S1.6, S1.7
unnamed: C12.1, R7.1, Z1.4 (-)
unnamed: C12.2, Z1.13 (FC)
unnamed: C13.1, R10.2, Z2.4 (-)
unnamed: C13.2, Z2.13 (FC)
unnamed: CR8.1 (+), S1.2
unnamed: CR8.2, J1.3
unnamed: CR8.3 (-), S1.1
unnamed: CR8.4, J1.1
unnamed: J1.2, S1.4
unnamed: Q3.1 (E), Q4.3 (C), R2.2, R3.2, R4.1
unnamed: Q3.2 (C), Q4.1 (B), R1.1
unnamed: Q3.3 (B), R2.1, Z1.10 (Vout)
unnamed: Q5.1 (E), R5.2, Z1.5 (+)
unnamed: Q5.2 (C), R9.1
unnamed: Q5.3 (B), R8.2
unnamed: Q6.1 (B), R16.1, Z2.11 (VC)
unnamed: Q6.3 (C), R17.1, R18.2, Z2.10 (Vout)
unnamed: R3.1, R9.2, Z1.2 (ILIM)
unnamed: R5.3, R6.2
unnamed: R6.1, Z1.6 (VREF)
unnamed: R10.1, R12.1
unnamed: R10.3, R13.2
unnamed: R5.1, R11.1
unnamed: R14.2, R17.2, Z2.2 (ILIM)
unnamed: R15.1, Z2.5 (+)
unnamed: R15.2, Z2.6 (VREF)
