Board-Folk/TRS80IUS/v1.1/Kicad/TRS80IUS_RAM.kicad_sch

## KiCad design v1.1/Kicad/TRS80IUS_RAM.kicad_sch (2023-12-29)

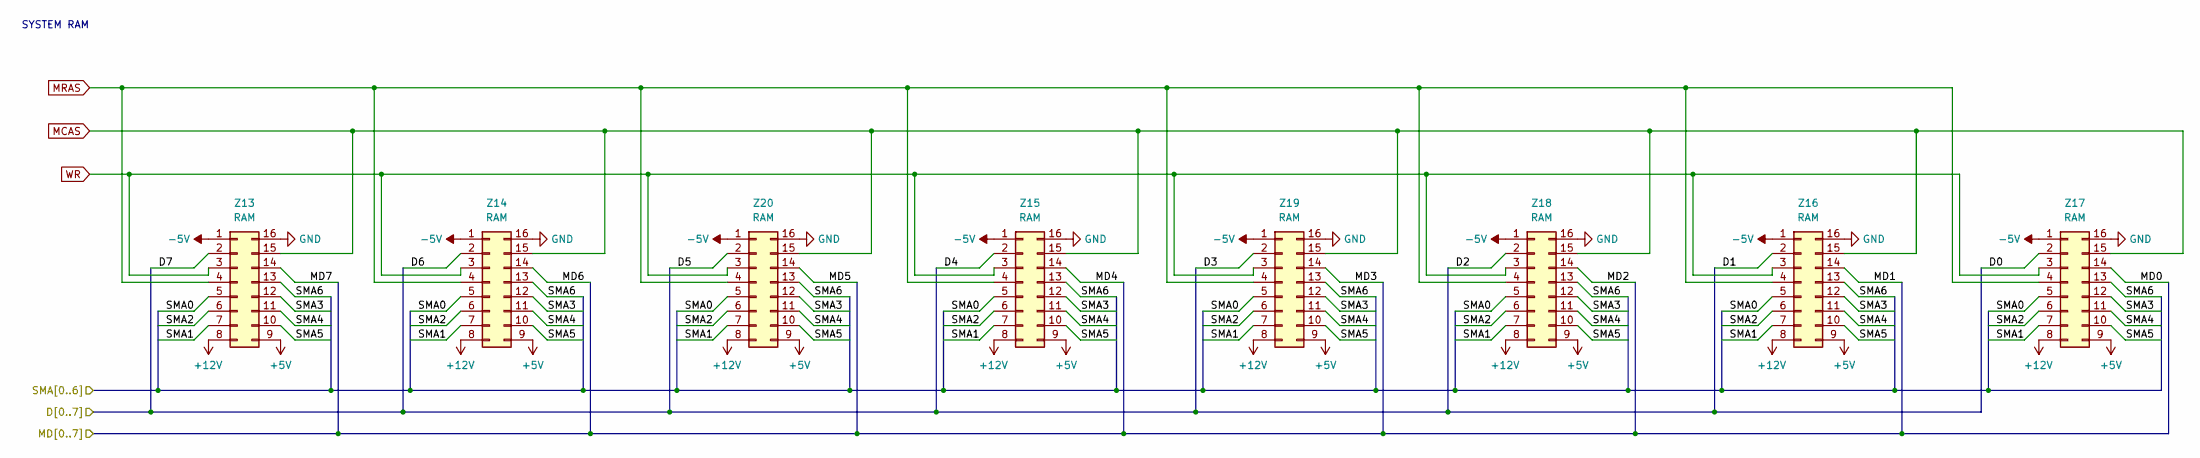
[picture p12: schematic TRS80IUS_RAM.kicad_sch]

Parts:
Z13, Z14, Z15, Z16, Z17, Z18, Z19, Z20: RAM; DIP-16_W7.62mm

Connections:
+5V: Z13.9, Z14.9, Z15.9, Z16.9, Z17.9, Z18.9, Z19.9, Z20.9
+12V: Z13.8, Z14.8, Z15.8, Z16.8, Z17.8, Z18.8, Z19.8, Z20.8
-5V: Z13.1, Z14.1, Z15.1, Z16.1, Z17.1, Z18.1, Z19.1, Z20.1
GND: Z13.16, Z14.16, Z15.16, Z16.16, Z17.16, Z18.16, Z19.16, Z20.16
MCAS: Z13.15, Z14.15, Z15.15, Z16.15, Z17.15, Z18.15, Z19.15, Z20.15
MRAS: Z13.4, Z14.4, Z15.4, Z16.4, Z17.4, Z18.4, Z19.4, Z20.4
WR: Z13.3, Z14.3, Z15.3, Z16.3, Z17.3, Z18.3, Z19.3, Z20.3

Notes on the sheet:
SYSTEM RAM
