Board-Folk/TRS80IUS/v1.1/Kicad/TRS80IUS_SPARE.kicad_sch

## KiCad design v1.1/Kicad/TRS80IUS_SPARE.kicad_sch (2023-12-29)

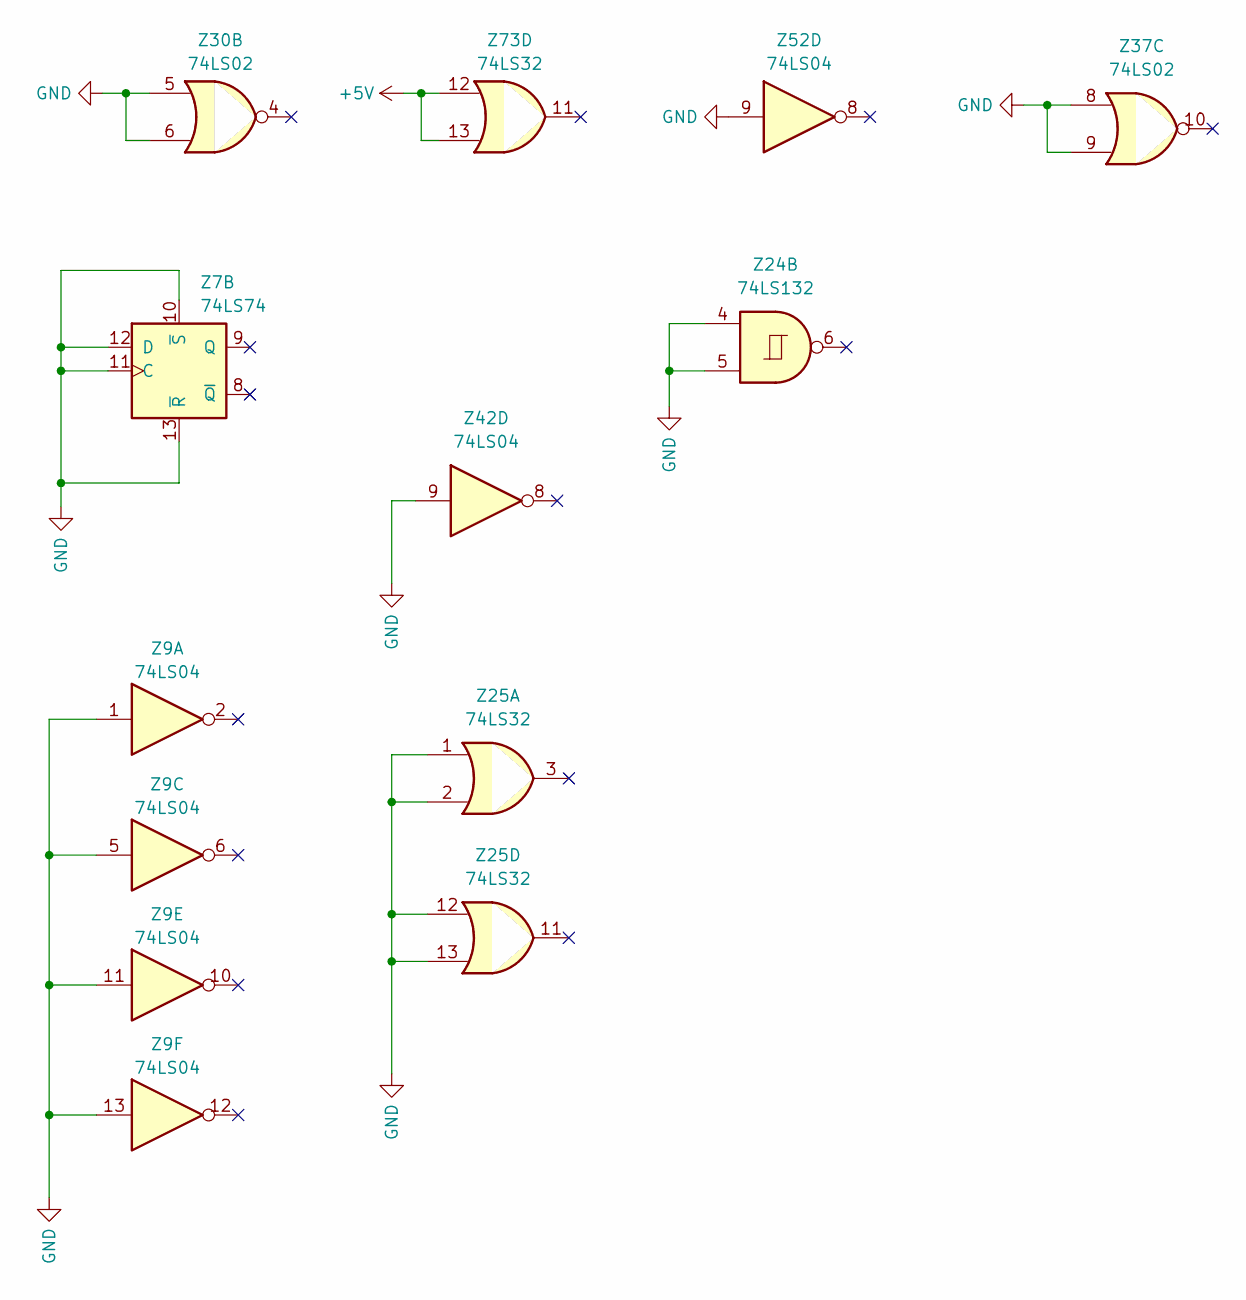
[picture p13: schematic TRS80IUS_SPARE.kicad_sch]

Parts:
Z7: 74LS74; DIP-14_W7.62mm
Z9, Z42, Z52: 74LS04; DIP-14_W7.62mm
Z24: 74LS132; DIP-14_W7.62mm
Z25, Z73: 74LS32; DIP-14_W7.62mm
Z30, Z37: 74LS02; DIP-14_W7.62mm

Connections:
+5V: Z73.12, Z73.13
GND: Z7.10 (~S), Z7.11 (C), Z7.12 (D), Z7.13 (~R), Z9.1, Z9.5, Z9.11, Z9.13, Z24.4, Z24.5, Z25.1, Z25.2, Z25.12, Z25.13, Z30.5, Z30.6, Z37.8, Z37.9, Z42.9, Z52.9
