Board-Folk/TRS80IUS/v1.1/Kicad/TRS80IUS_TAPE.kicad_sch

## KiCad design v1.1/Kicad/TRS80IUS_TAPE.kicad_sch (2023-12-29)

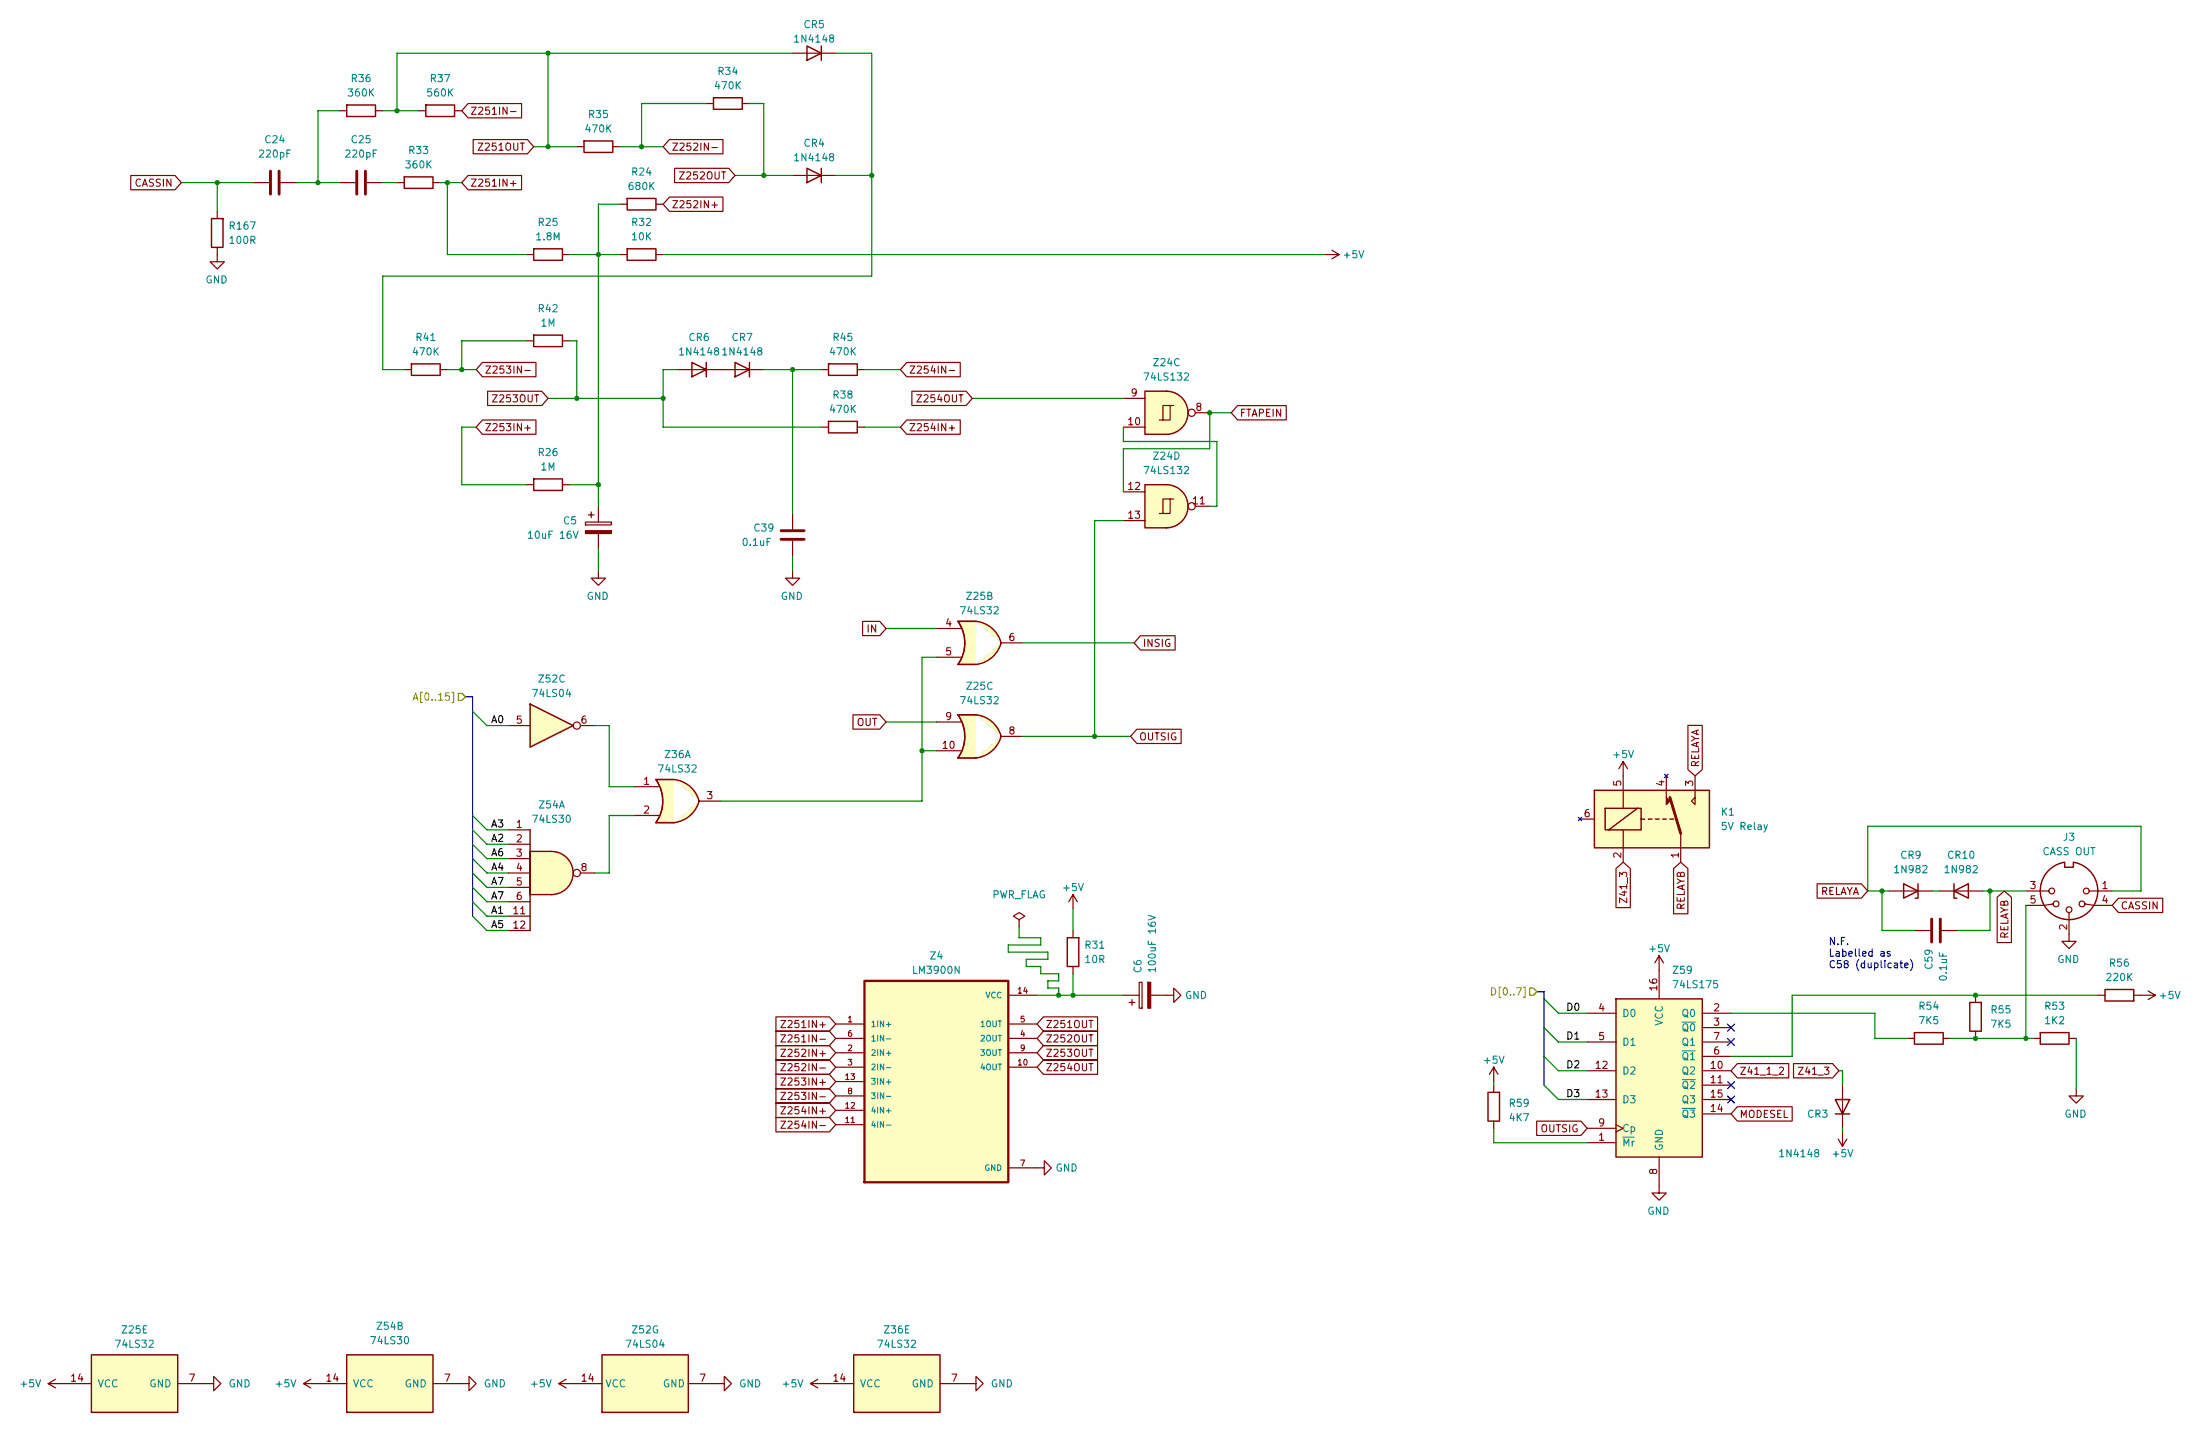
[picture p14: schematic TRS80IUS_TAPE.kicad_sch]

Parts:
C5: 10uF 16V; Electrolytic Cap 2.5mm
C6: 100uF 16V; Electrolytic Cap 5.08mm
C24, C25: 220pF; Ceramic Disc 6.35mm
C39: 0.1uF; Ceramic Disc 6.35mm
C59: 0.1uF; Ceramic Disc 9.78mm
CR3, CR4, CR5, CR6, CR7: 1N4148; Diode 12.7mm
CR9, CR10: 1N982; Diode 12.7mm
J3: CASS OUT; 5-Pin DIN Socket - J3
K1: 5V Relay; K1
R24: 680K; Resistor 12.7mm
R25: 1.8M; Resistor 12.7mm
R26, R42: 1M; Resistor 12.7mm
R31: 10R; Resistor 12.7mm
R32: 10K; Resistor 12.7mm
R33, R36: 360K; Resistor 12.7mm
R34, R35, R38, R41, R45: 470K; Resistor 12.7mm
R37: 560K; Resistor 12.7mm
R53: 1K2; Resistor 12.7mm
R54, R55: 7K5; Resistor 12.7mm
R56: 220K; Resistor 12.7mm
R59: 4K7; Resistor 12.7mm
R167: 100R; Resistor R167
Z4: LM3900N; DIP-14_W7.62mm
Z24: 74LS132; DIP-14_W7.62mm
Z25, Z36: 74LS32; DIP-14_W7.62mm
Z52: 74LS04; DIP-14_W7.62mm
Z54: 74LS30; DIP-14_W7.62mm
Z59: 74LS175; DIP-16_W7.62mm

Connections:
+5V: CR3.1 (K), K1.5, R31.2, R32.1, R56.2, R59.2, Z25.14 (VCC), Z36.14 (VCC), Z52.14 (VCC), Z54.14 (VCC), Z59.16 (VCC)
A0: Z52.5
A1: Z54.11
A2: Z54.2
A3: Z54.1
A4: Z54.4
A5: Z54.12
A6: Z54.3
A7: Z54.5, Z54.6
CASSIN: C24.1, J3.4, R167.2
D0: Z59.4 (D0)
D1: Z59.5 (D1)
D2: Z59.12 (D2)
D3: Z59.13 (D3)
FTAPEIN: Z24.8, Z24.12
GND: C5.2, C6.2, C39.1, J3.2, R53.1, R167.1, Z4.7 (GND), Z25.7 (GND), Z36.7 (GND), Z52.7 (GND), Z54.7 (GND), Z59.8 (GND)
IN: Z25.4
INSIG: Z25.6
MODESEL: Z59.14 (~Q3)
unnamed: C5.1, R24.2, R25.1, R26.1, R32.2
unnamed: C6.1, R31.1, Z4.14 (VCC)
unnamed: C24.2, C25.1, R36.2
unnamed: C25.2, R33.2
unnamed: C39.2, CR7.1 (K), R45.2
unnamed: CR4.1 (K), CR5.1 (K), R41.2
unnamed: CR6.1 (K), CR7.2 (A)
unnamed: CR9.1 (K), CR10.1 (K)
unnamed: J3.5, R53.2, R54.1, R55.1
unnamed: R54.2, Z59.2 (Q0)
unnamed: R55.2, R56.1, Z59.6 (~Q1)
unnamed: R59.1, Z59.1 (~Mr)
unnamed: Z24.10, Z24.11
unnamed: Z25.5, Z25.10, Z36.3
unnamed: Z36.1, Z52.6
unnamed: Z36.2, Z54.8
OUT: Z25.9
OUTSIG: Z24.13, Z25.8, Z59.9 (Cp)
RELAYA: C59.2, CR9.2 (A), J3.1, K1.3
RELAYB: C59.1, CR10.2 (A), J3.3, K1.1
Z41_1_2: Z59.10 (Q2)
Z41_3: CR3.2 (A), K1.2
Z251IN+: R25.2, R33.1, Z4.1 (1IN+)
Z251IN-: R37.1, Z4.6 (1IN-)
Z251OUT: CR5.2 (A), R35.2, R36.1, R37.2, Z4.5 (1OUT)
Z252IN+: R24.1, Z4.2 (2IN+)
Z252IN-: R34.2, R35.1, Z4.3 (2IN-)
Z252OUT: CR4.2 (A), R34.1, Z4.4 (2OUT)
Z253IN+: R26.2, Z4.13 (3IN+)
Z253IN-: R41.1, R42.2, Z4.8 (3IN-)
Z253OUT: CR6.2 (A), R38.2, R42.1, Z4.9 (3OUT)
Z254IN+: R38.1, Z4.12 (4IN+)
Z254IN-: R45.1, Z4.11 (4IN-)
Z254OUT: Z4.10 (4OUT), Z24.9

Notes on the sheet:
N.F. Labelled as C58 (duplicate)
