Board-Folk/TRS80IUS/v1.1/Kicad/TRS80IUS_TIMING.kicad_sch

## KiCad design v1.1/Kicad/TRS80IUS_TIMING.kicad_sch (2023-12-29)

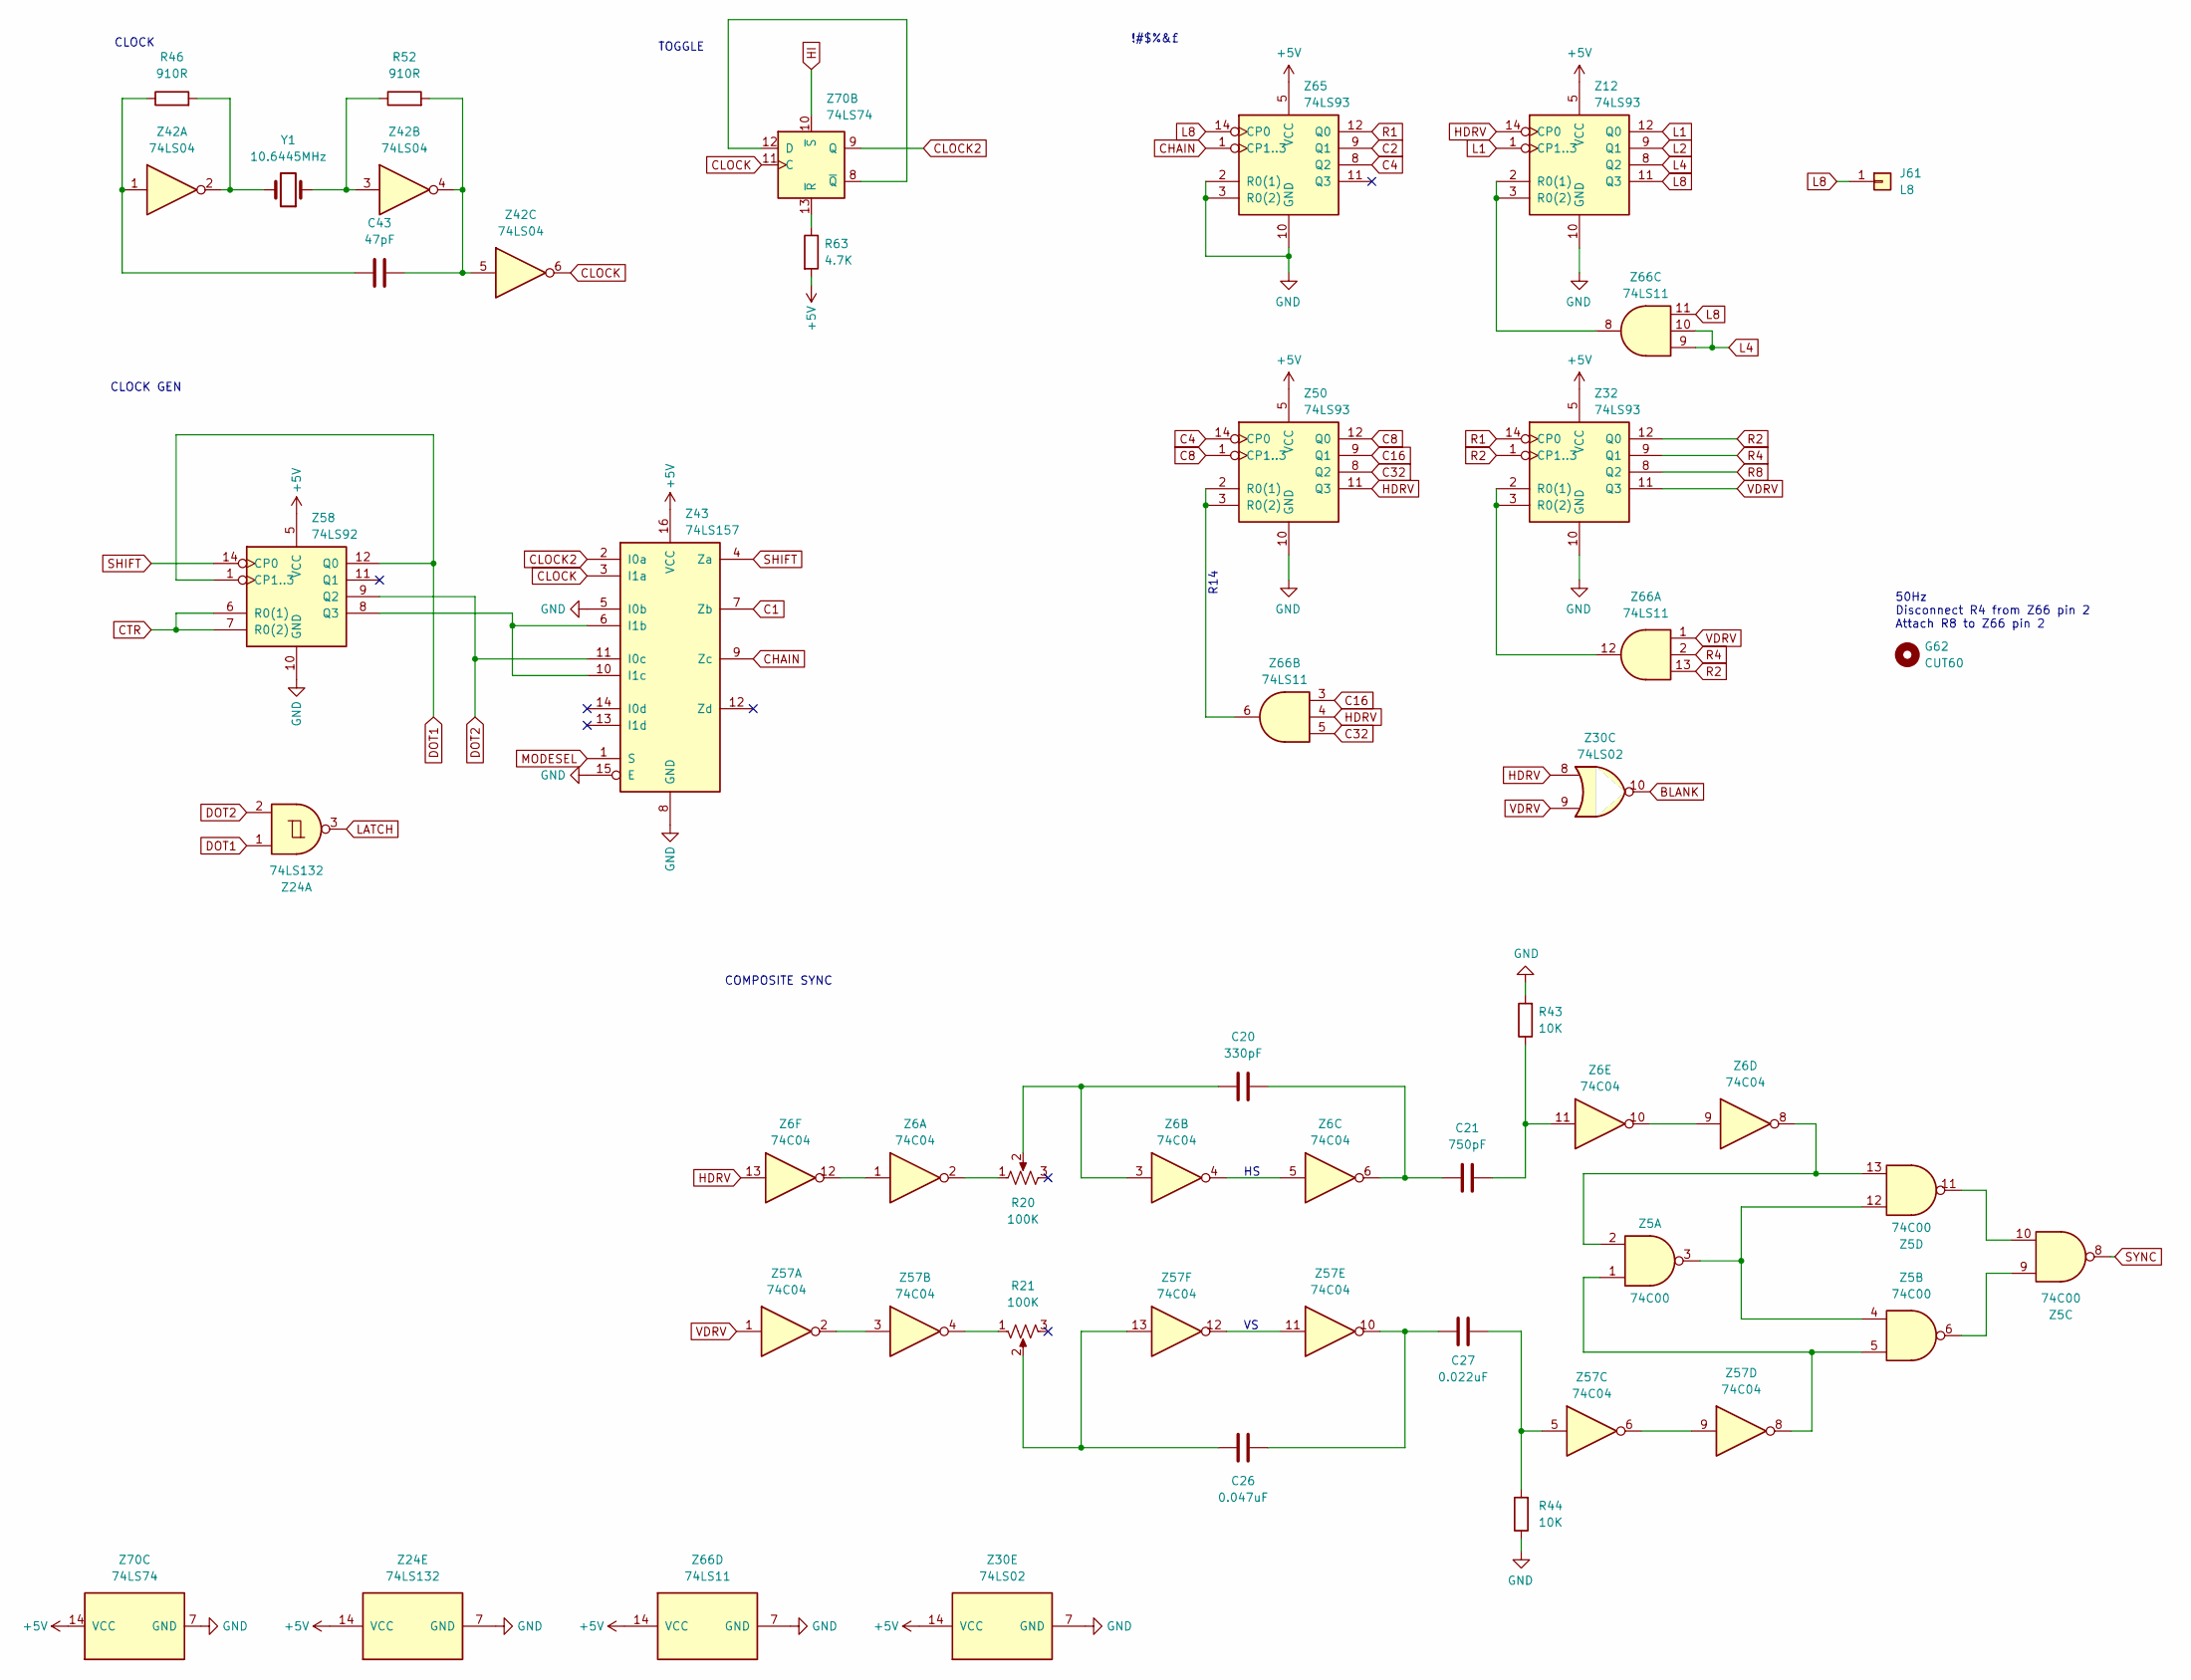
[picture p15: schematic TRS80IUS_TIMING.kicad_sch]

Parts:
C20: 330pF; Ceramic Disc 6.35mm
C21: 750pF; Ceramic Disc 6.35mm
C26: 0.047uF; Poly 6.35mm
C27: 0.022uF; Poly 5.08mm
C43: 47pF; Ceramic Disc 6.35mm
G62: CUT60; CUT
J61: L8; MODHEADER
R20, R21: 100K; Pot
R43, R44: 10K; Resistor 12.7mm
R46, R52: 910R; Resistor 12.7mm
R63: 4.7K; Resistor 12.7mm
Y1: 10.6445MHz; Crystal 5.08mm
Z5: 74C00; DIP-14_W7.62mm
Z6, Z57: 74C04; DIP-14_W7.62mm
Z12, Z32, Z50, Z65: 74LS93; DIP-14_W7.62mm
Z24: 74LS132; DIP-14_W7.62mm
Z30: 74LS02; DIP-14_W7.62mm
Z42: 74LS04; DIP-14_W7.62mm
Z43: 74LS157; DIP-16_W7.62mm
Z58: 74LS92; DIP-14_W7.62mm
Z66: 74LS11; DIP-14_W7.62mm
Z70: 74LS74; DIP-14_W7.62mm

Connections:
+5V: R63.2, Z12.5 (VCC), Z24.14 (VCC), Z30.14 (VCC), Z32.5 (VCC), Z43.16 (VCC), Z50.5 (VCC), Z58.5 (VCC), Z65.5 (VCC), Z66.14 (VCC), Z70.14 (VCC)
BLANK: Z30.10
C1: Z43.7 (Zb)
C2: Z65.9 (Q1)
C4: Z50.14 (CP0), Z65.8 (Q2)
C8: Z50.1 (CP1..3), Z50.12 (Q0)
C16: Z50.9 (Q1), Z66.3
C32: Z50.8 (Q2), Z66.5
CHAIN: Z43.9 (Zc), Z65.1 (CP1..3)
CLOCK: Z42.6, Z43.3 (I1a), Z70.11 (C)
CLOCK2: Z43.2 (I0a), Z70.9 (Q)
CTR: Z58.6 (R0(1)), Z58.7 (R0(2))
DOT1: Z24.1, Z58.1 (CP1..3), Z58.12 (Q0)
DOT2: Z24.2, Z43.11 (I0c), Z58.9 (Q2)
GND: R43.2, R44.1, Z12.10 (GND), Z24.7 (GND), Z30.7 (GND), Z32.10 (GND), Z43.5 (I0b), Z43.8 (GND), Z43.15 (E), Z50.10 (GND), Z58.10 (GND), Z65.2 (R0(1)), Z65.3 (R0(2)), Z65.10 (GND), Z66.7 (GND), Z70.7 (GND)
HDRV: Z6.13, Z12.14 (CP0), Z30.8, Z50.11 (Q3), Z66.4
HI: Z70.10 (~S)
L1: Z12.1 (CP1..3), Z12.12 (Q0)
L2: Z12.9 (Q1)
L4: Z12.8 (Q2), Z66.9, Z66.10
L8: J61.1, Z12.11 (Q3), Z65.14 (CP0), Z66.11
LATCH: Z24.3
MODESEL: Z43.1 (S)
unnamed: C20.1, R20.2, Z6.3
unnamed: C20.2, C21.1, Z6.6
unnamed: C21.2, R43.1, Z6.11
unnamed: C26.1, R21.2, Z57.13
unnamed: C26.2, C27.1, Z57.10
unnamed: C27.2, R44.2, Z57.5
unnamed: C43.1, R46.1, Z42.1
unnamed: C43.2, R52.2, Z42.4, Z42.5
unnamed: R20.1, Z6.2
unnamed: R21.1, Z57.4
unnamed: R46.2, Y1.2, Z42.2
unnamed: R52.1, Y1.1, Z42.3
unnamed: R63.1, Z70.13 (~R)
unnamed: Z5.1, Z5.5, Z57.8
unnamed: Z5.6, Z5.9
unnamed: Z5.10, Z5.11
unnamed: Z5.3, Z5.4, Z5.12
unnamed: Z5.2, Z5.13, Z6.8
unnamed: Z6.1, Z6.12
unnamed: Z6.4, Z6.5
unnamed: Z6.9, Z6.10
unnamed: Z12.2 (R0(1)), Z12.3 (R0(2)), Z66.8
unnamed: Z32.2 (R0(1)), Z32.3 (R0(2)), Z66.12
unnamed: Z43.6 (I1b), Z43.10 (I1c), Z58.8 (Q3)
unnamed: Z50.2 (R0(1)), Z50.3 (R0(2)), Z66.6
unnamed: Z57.2, Z57.3
unnamed: Z57.6, Z57.9
unnamed: Z57.11, Z57.12
unnamed: Z70.8 (~Q), Z70.12 (D)
R1: Z32.14 (CP0), Z65.12 (Q0)
R2: Z32.1 (CP1..3), Z32.12 (Q0), Z66.13
R4: Z32.9 (Q1), Z66.2
R8: Z32.8 (Q2)
SHIFT: Z43.4 (Za), Z58.14 (CP0)
SYNC: Z5.8
VDRV: Z30.9, Z32.11 (Q3), Z57.1, Z66.1

Notes on the sheet:
CLOCK
TOGGLE
50Hz Disconnect R4 from Z66 pin 2 Attach R8 to Z66 pin 2
CLOCK GEN
R14
!#$%&£
COMPOSITE SYNC
