Board-Folk/TRS80IUS/v1.1/Kicad/TRS80IUS_VIDEO.kicad_sch

## KiCad design v1.1/Kicad/TRS80IUS_VIDEO.kicad_sch (2023-12-29)

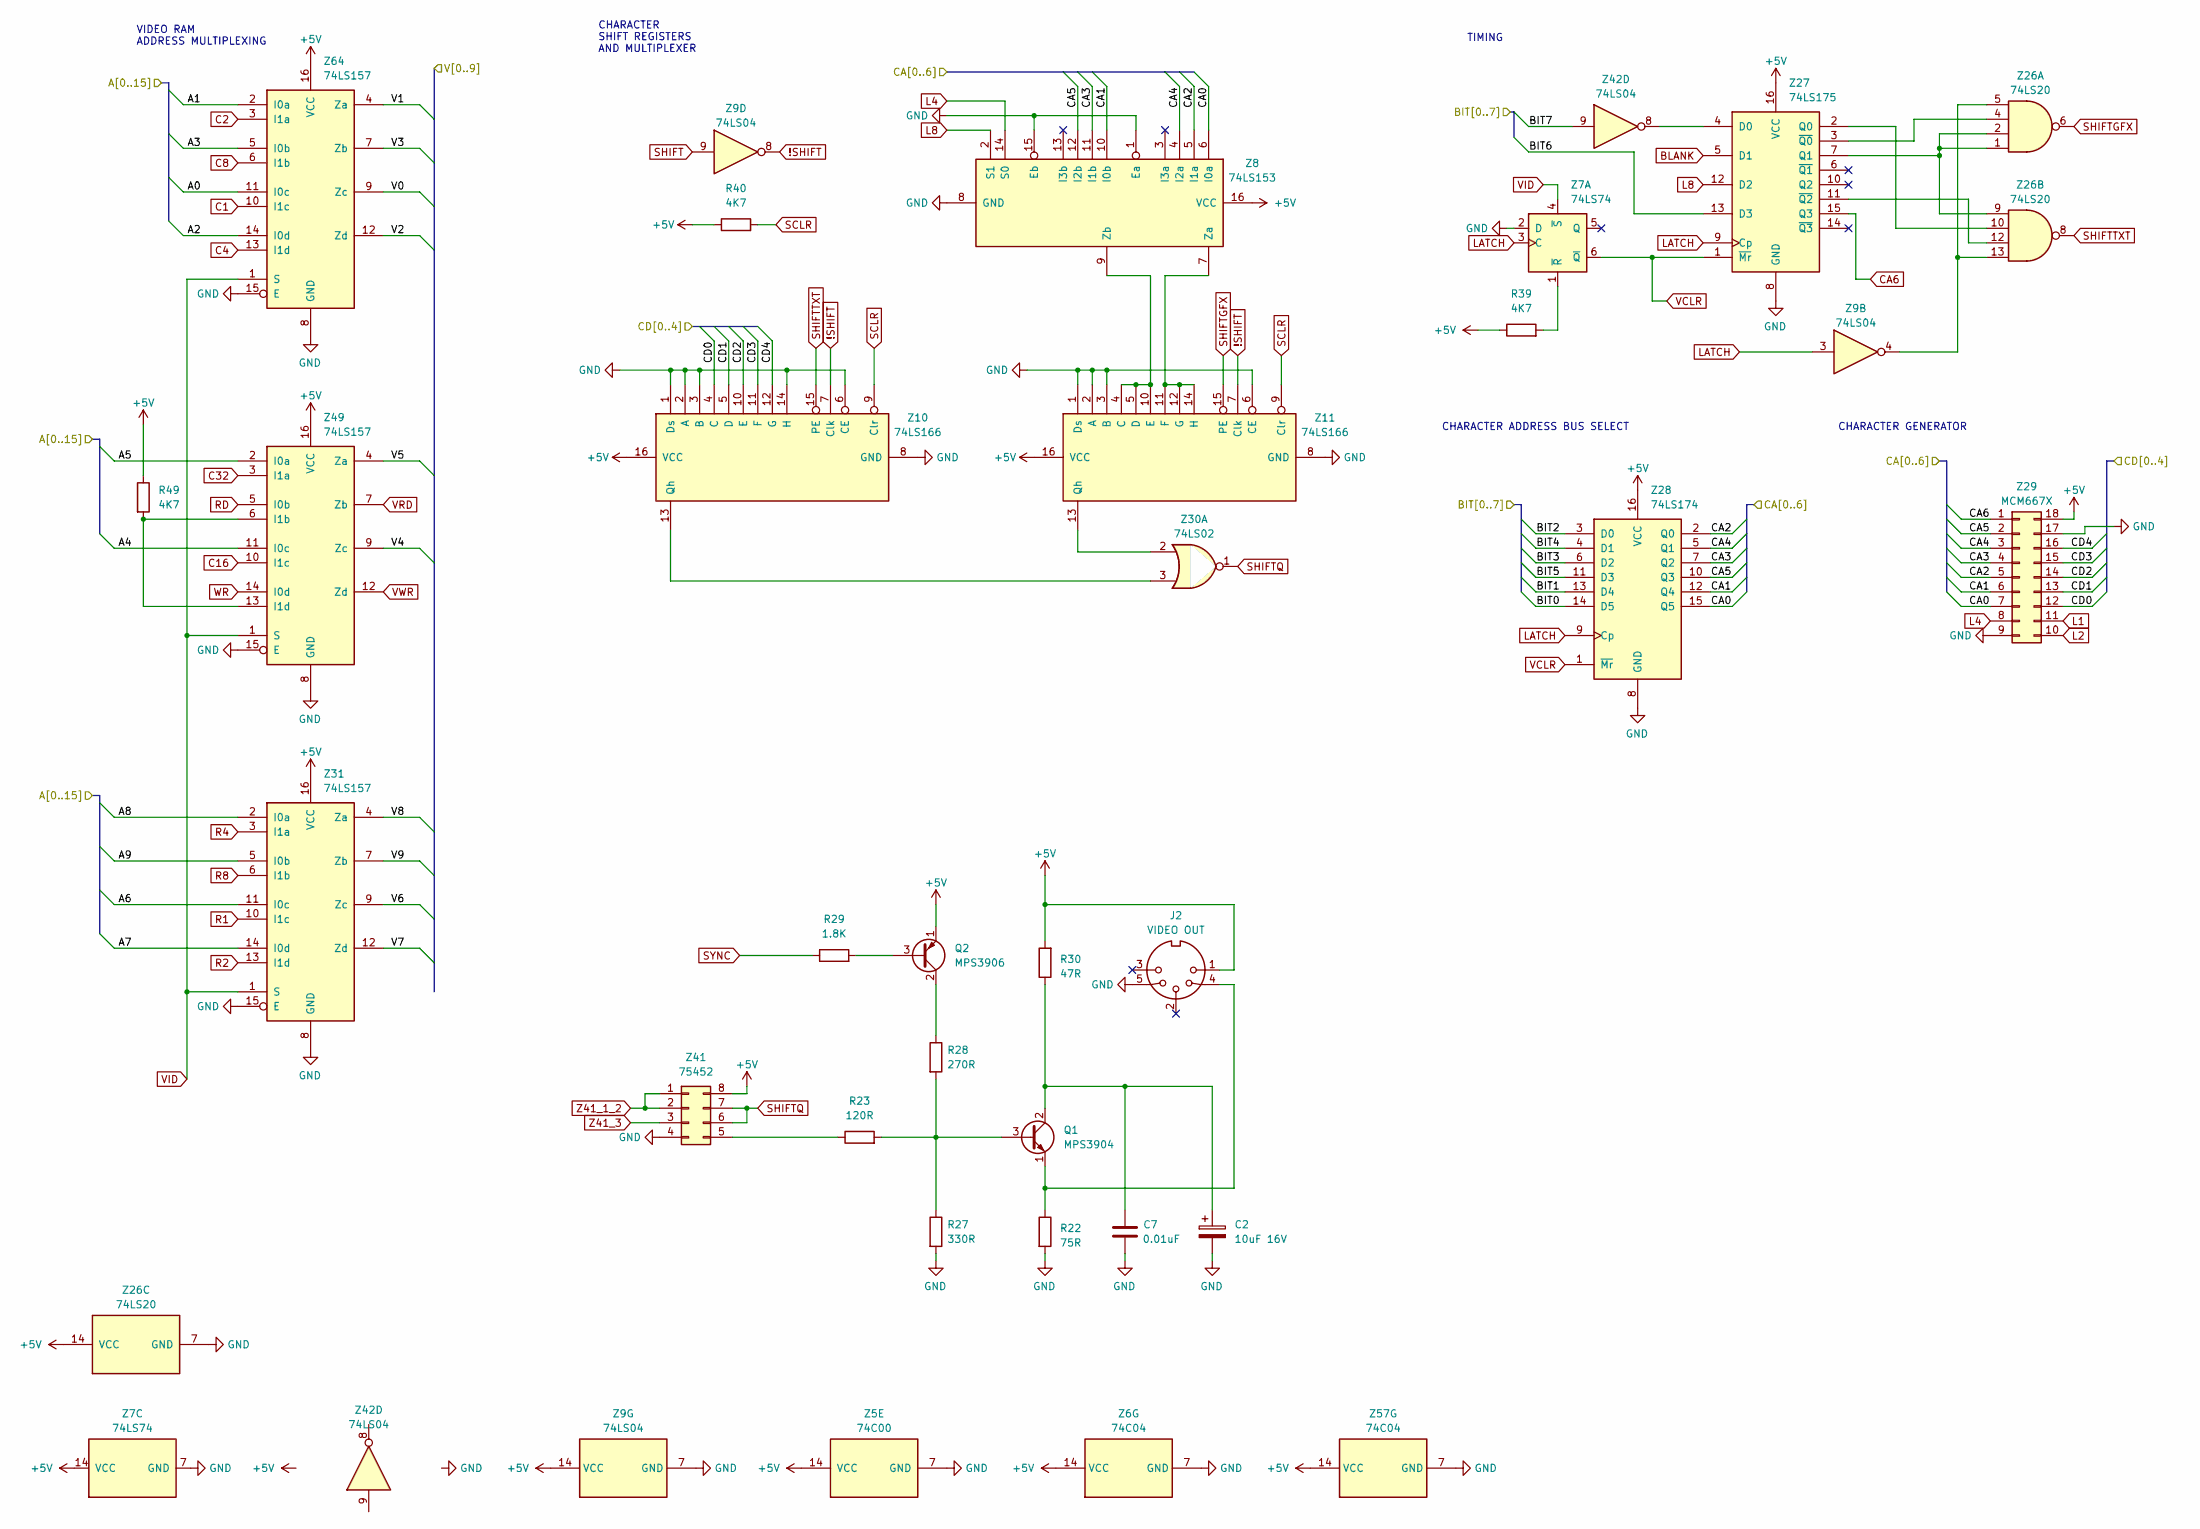
[picture p16: schematic TRS80IUS_VIDEO.kicad_sch]

Parts:
C2: 10uF 16V; Electrolytic Cap 2.5mm
C7: 0.01uF; Ceramic Disc 6.35mm
J2: VIDEO OUT; 5-Pin DIN Socket - J2
Q1: MPS3904; Transistor
Q2: MPS3906; Transistor
R22: 75R; Resistor 12.7mm
R23: 120R; Resistor 12.7mm
R27: 330R; Resistor 12.7mm
R28: 270R; Resistor 12.7mm
R29: 1.8K; Resistor 12.7mm
R30: 47R; Resistor 12.7mm
R39, R40, R49: 4K7; Resistor 12.7mm
Z5: 74C00; DIP-14_W7.62mm
Z6, Z57: 74C04; DIP-14_W7.62mm
Z7: 74LS74; DIP-14_W7.62mm
Z8: 74LS153; DIP-16_W7.62mm
Z9, Z42: 74LS04; DIP-14_W7.62mm
Z10, Z11: 74LS166; DIP-16_W7.62mm
Z26: 74LS20; DIP-14_W7.62mm
Z27: 74LS175; DIP-16_W7.62mm
Z28: 74LS174; DIP-16_W7.62mm
Z29: MCM667X; DIP-18_W7.62mm
Z30: 74LS02; DIP-14_W7.62mm
Z31, Z49, Z64: 74LS157; DIP-16_W7.62mm
Z41: 75452; DIP-8_W7.62mm

Connections:
!SHIFT: Z9.8, Z10.7 (Clk), Z11.7 (Clk)
+5V: J2.1, Q2.1 (E), R30.2, R39.1, R40.1, R49.1, Z5.14 (VCC), Z6.14 (VCC), Z7.14 (VCC), Z8.16 (VCC), Z9.14 (VCC), Z10.16 (VCC), Z11.16 (VCC), Z26.14 (VCC), Z27.16 (VCC), Z28.16 (VCC), Z29.18, Z31.16 (VCC), Z41.8, Z49.16 (VCC), Z57.14 (VCC), Z64.16 (VCC)
A0: Z64.11 (I0c)
A1: Z64.2 (I0a)
A2: Z64.14 (I0d)
A3: Z64.5 (I0b)
A4: Z49.11 (I0c)
A5: Z49.2 (I0a)
A6: Z31.11 (I0c)
A7: Z31.14 (I0d)
A8: Z31.2 (I0a)
A9: Z31.5 (I0b)
BIT0: Z28.14 (D5)
BIT1: Z28.13 (D4)
BIT2: Z28.3 (D0)
BIT3: Z28.6 (D2)
BIT4: Z28.4 (D1)
BIT5: Z28.11 (D3)
BIT6: Z27.13 (D3)
BIT7: Z42.9
BLANK: Z27.5 (D1)
C1: Z64.10 (I1c)
C2: Z64.3 (I1a)
C4: Z64.13 (I1d)
C8: Z64.6 (I1b)
C16: Z49.10 (I1c)
C32: Z49.3 (I1a)
CA0: Z8.6 (I0a), Z28.15 (Q5), Z29.7
CA1: Z8.10 (I0b), Z28.12 (Q4), Z29.6
CA2: Z8.5 (I1a), Z28.2 (Q0), Z29.5
CA3: Z8.11 (I1b), Z28.7 (Q2), Z29.4
CA4: Z8.4 (I2a), Z28.5 (Q1), Z29.3
CA5: Z8.12 (I2b), Z28.10 (Q3), Z29.2
CA6: Z27.15 (Q3), Z29.1
CD0: Z10.4 (C), Z29.12
CD1: Z10.5 (D), Z29.13
CD2: Z10.10 (E), Z29.14
CD3: Z10.11 (F), Z29.15
CD4: Z10.12 (G), Z29.16
GND: C2.2, C7.2, J2.5, R22.2, R27.2, Z5.7 (GND), Z6.7 (GND), Z7.2 (D), Z7.7 (GND), Z8.1 (Ea), Z8.8 (GND), Z8.15 (Eb), Z9.7 (GND), Z10.1 (Ds), Z10.2 (A), Z10.3 (B), Z10.6 (CE), Z10.8 (GND), Z10.14 (H), Z11.1 (Ds), Z11.2 (A), Z11.3 (B), Z11.6 (CE), Z11.8 (GND), Z26.7 (GND), Z27.8 (GND), Z28.8 (GND), Z29.9, Z29.17, Z31.8 (GND), Z31.15 (E), Z41.4, Z49.8 (GND), Z49.15 (E), Z57.7 (GND), Z64.8 (GND), Z64.15 (E)
L1: Z29.11
L2: Z29.10
L4: Z8.14 (S0), Z29.8
L8: Z8.2 (S1), Z27.12 (D2)
LATCH: Z7.3 (C), Z9.3, Z27.9 (Cp), Z28.9 (Cp)
unnamed: C2.1, C7.1, Q1.2 (C), R30.1
unnamed: J2.4, Q1.1 (E), R22.1
unnamed: Q1.3 (B), R23.2, R27.1, R28.2
unnamed: Q2.2 (C), R28.1
unnamed: Q2.3 (B), R29.2
unnamed: R23.1, Z41.5
unnamed: R39.2, Z7.1 (~R)
unnamed: R49.2, Z49.6 (I1b), Z49.13 (I1d)
unnamed: Z10.13 (Qh), Z30.3
unnamed: Z8.9 (Zb), Z11.4 (C), Z11.5 (D), Z11.10 (E)
unnamed: Z8.7 (Za), Z11.11 (F), Z11.12 (G), Z11.14 (H)
unnamed: Z11.13 (Qh), Z30.2
unnamed: Z26.1, Z26.2, Z26.9, Z27.7 (Q1)
unnamed: Z26.4, Z27.3 (~Q0)
unnamed: Z26.10, Z27.2 (Q0)
unnamed: Z26.12, Z27.11 (~Q2)
unnamed: Z9.4, Z26.5, Z26.13
unnamed: Z27.4 (D0), Z42.8
R1: Z31.10 (I1c)
R2: Z31.13 (I1d)
R4: Z31.3 (I1a)
R8: Z31.6 (I1b)
RD: Z49.5 (I0b)
SCLR: R40.2, Z10.9 (Clr), Z11.9 (Clr)
SHIFT: Z9.9
SHIFTGFX: Z11.15 (PE), Z26.6
SHIFTQ: Z30.1, Z41.6, Z41.7
SHIFTTXT: Z10.15 (PE), Z26.8
SYNC: R29.1
V0: Z64.9 (Zc)
V1: Z64.4 (Za)
V2: Z64.12 (Zd)
V3: Z64.7 (Zb)
V4: Z49.9 (Zc)
V5: Z49.4 (Za)
V6: Z31.9 (Zc)
V7: Z31.12 (Zd)
V8: Z31.4 (Za)
V9: Z31.7 (Zb)
VCLR: Z7.6 (~Q), Z27.1 (~Mr), Z28.1 (~Mr)
VID: Z7.4 (~S), Z31.1 (S), Z49.1 (S), Z64.1 (S)
VRD: Z49.7 (Zb)
VWR: Z49.12 (Zd)
WR: Z49.14 (I0d)
Z41_1_2: Z41.1, Z41.2
Z41_3: Z41.3

Notes on the sheet:
VIDEO RAM ADDRESS MULTIPLEXING
TIMING
CHARACTER SHIFT REGISTERS AND MULTIPLEXER
CHARACTER GENERATOR
CHARACTER ADDRESS BUS SELECT
